openbikesensor/OpenBikeSensor3dPrintableCase/render/thumbnails/LiteCase/LiteSensorSpacer.png

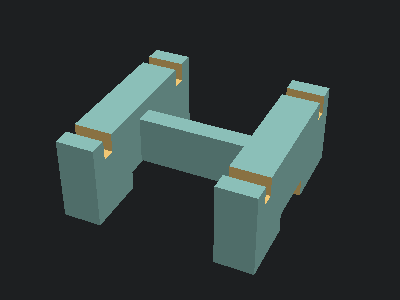
render/thumbnails/LiteCase/LiteSensorSpacer.png
