openbikesensor/OpenBikeSensor3dPrintableCase/MainCase/VerticalCase_JSN-AJ/OBS-MainCase-B-001b_inner_logo_part.stl

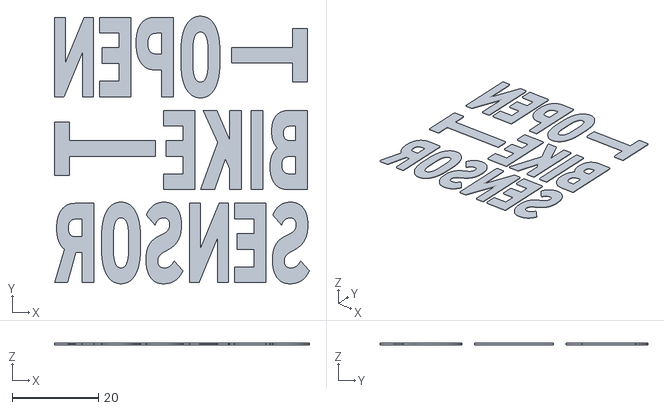
[picture p32: CAD file, 2021-05-19]
MainCase/VerticalCase_JSN-AJ/OBS-MainCase-B-001b_inner_logo_part.stl
59.2 x 62.2 x 0.4
