openbikesensor/OpenBikeSensor3dPrintableCase/MainCase/VerticalCase_JSN-AJ/OBS-MainCase-A-004_GPS-Cover_v0.1.2.stl

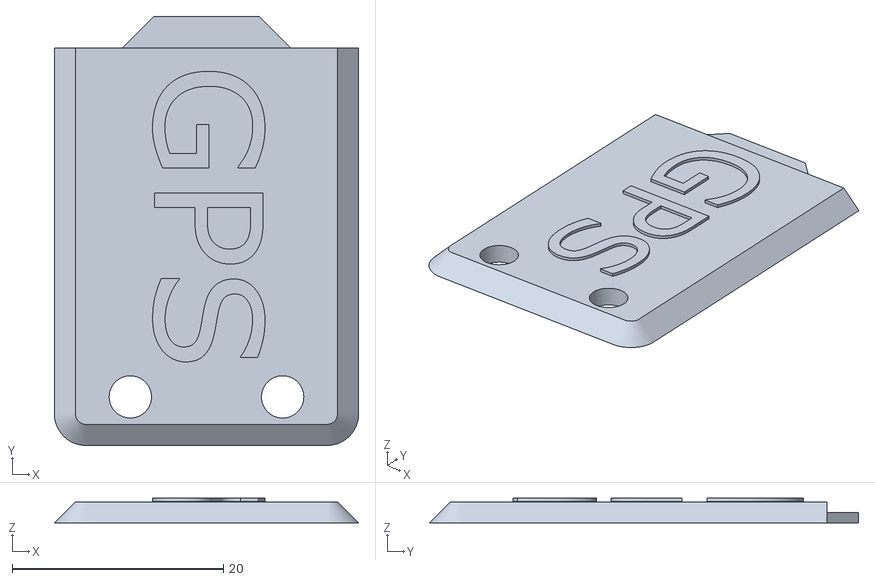
[picture p33: CAD file, 2021-04-24]
MainCase/VerticalCase_JSN-AJ/OBS-MainCase-A-004_GPS-Cover_v0.1.2.stl
28.8 x 40.6 x 2.36
