openbikesensor/OpenBikeSensor3dPrintableCase/MainCase/VerticalCase_JSN-AJ/OBS-MainCase-A-003_USB-Cover_v0.1.1.stl

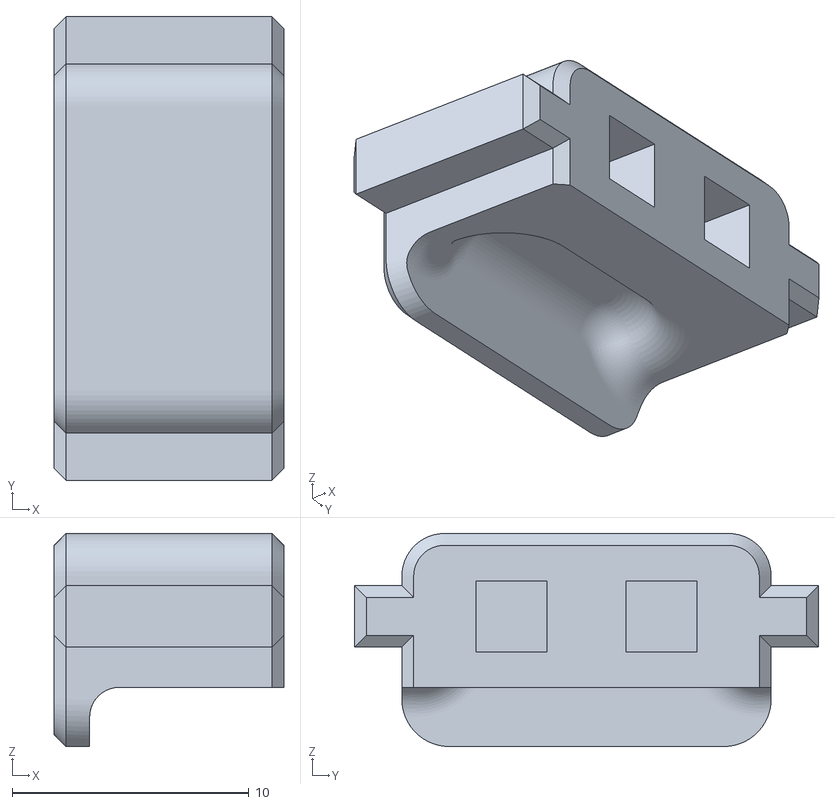
[picture p35: CAD file, 2021-03-09]
MainCase/VerticalCase_JSN-AJ/OBS-MainCase-A-003_USB-Cover_v0.1.1.stl
9.70 x 19.6 x 9.00
