openbikesensor/OpenBikeSensor3dPrintableCase/DisplayCase/DisplayCase32mm/Zwischenstueck.stl

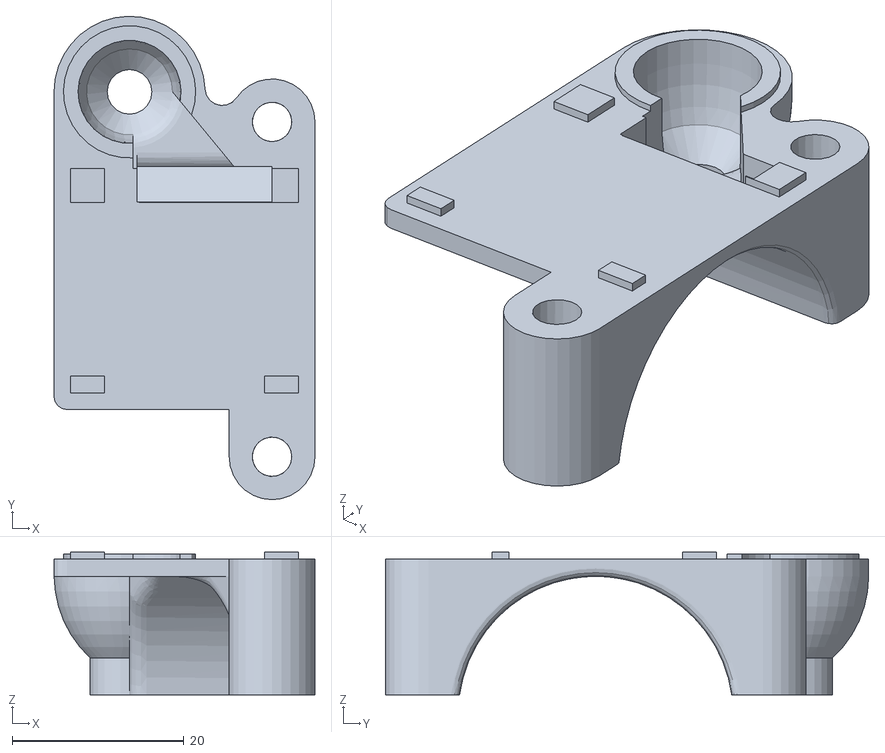
[picture p36: CAD file, 2020-05-23]
DisplayCase/DisplayCase32mm/Zwischenstueck.stl
30.4 x 56.3 x 16.6
