openbikesensor/OpenBikeSensor3dPrintableCase/DisplayCase/experimental/OBS-Kabelbinder-Adapter_kompatibel_zu_OBS-D-003v10.stp

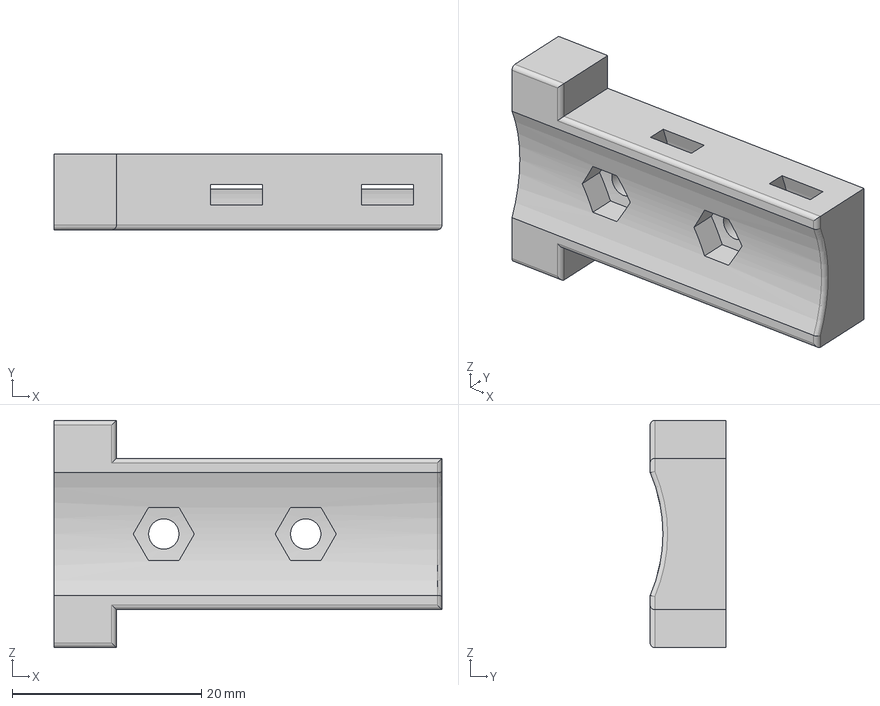
[picture p37: CAD file, 2021-03-13]
DisplayCase/experimental/OBS-Kabelbinder-Adapter_kompatibel_zu_OBS-D-003v10.stp
41.0 x 8.00 x 24.0 mm
