openbikesensor/OpenBikeSensor3dPrintableCase/DisplayCase/PermanentlyMounted/OBS-D-002-V1.step

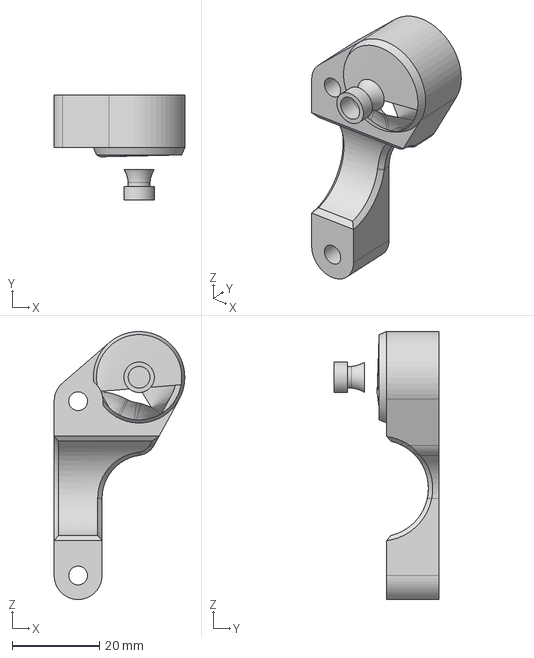
[picture p38: CAD file, 2020-04-30]
DisplayCase/PermanentlyMounted/OBS-D-002-V1.step
30.0 x 24.0 x 61.5 mm
