openbikesensor/OpenBikeSensor3dPrintableCase/DisplayCase/SlideOnDisplay/OBS-Display-A-005_Kabelbinder_Schiene_v0.1.1.stp

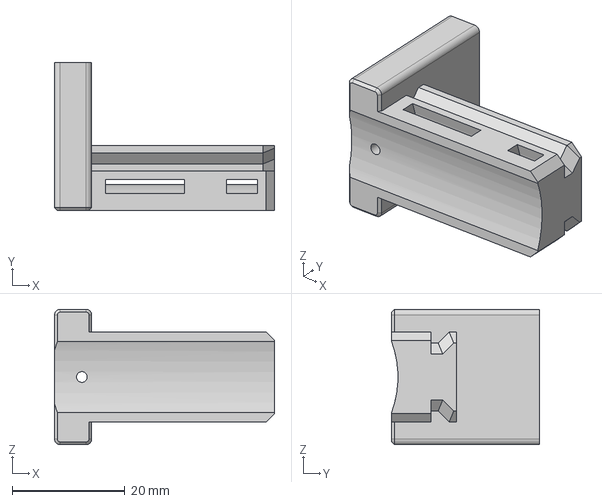
[picture p39: CAD file, 2021-06-07]
DisplayCase/SlideOnDisplay/OBS-Display-A-005_Kabelbinder_Schiene_v0.1.1.stp
39.0 x 26.2 x 24.0 mm
