openbikesensor/OpenBikeSensor3dPrintableCase/DisplayCase/SnapInDisplay/DisplayClip22_2_4mmbrake.stl

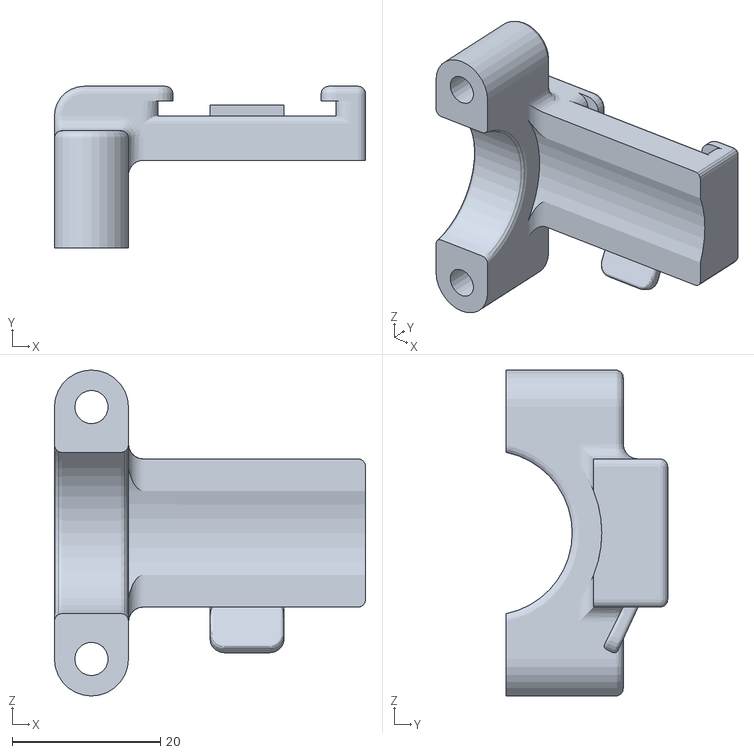
[picture p40: CAD file, 2020-10-29]
DisplayCase/SnapInDisplay/DisplayClip22_2_4mmbrake.stl
42.0 x 21.8 x 44.0
