openbikesensor/OpenBikeSensor3dPrintableCase/export/Calibration/HexNuts.stl

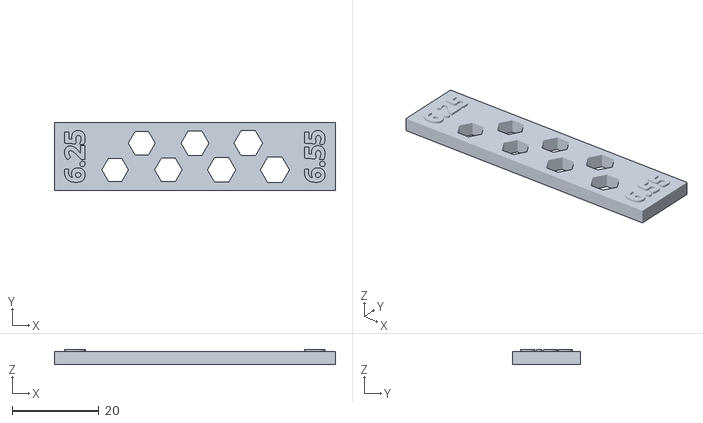
[picture p41: CAD file, 2022-03-04]
export/Calibration/HexNuts.stl
64.9 x 15.7 x 3.50
