openbikesensor/OpenBikeSensor3dPrintableCase/export/DisplayCase/DisplayCaseBottom.stl

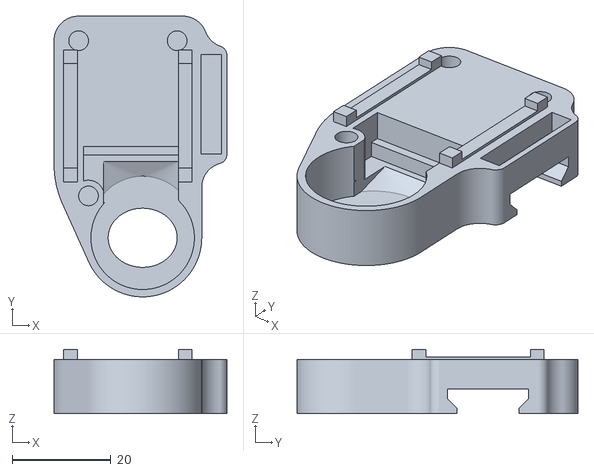
[picture p42: CAD file, 2023-01-06]
export/DisplayCase/DisplayCaseBottom.stl
35.1 x 57.0 x 13.0
