openbikesensor/OpenBikeSensor3dPrintableCase/export/Mounting/BikeRackMountSide.stl

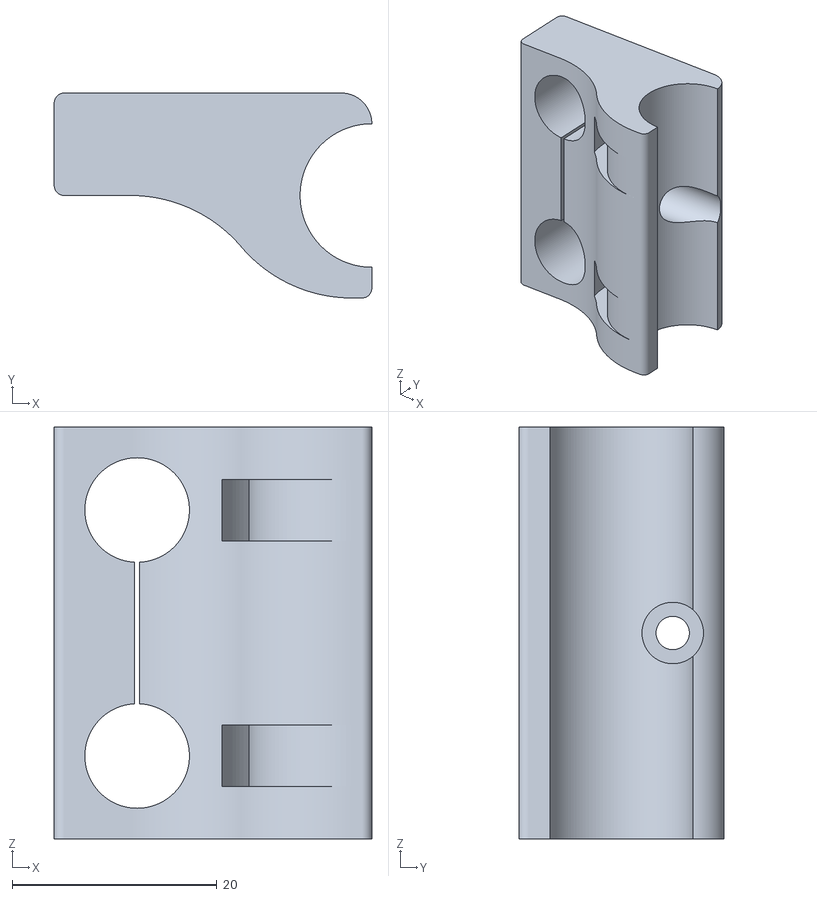
[picture p43: CAD file, 2023-01-06]
export/Mounting/BikeRackMountSide.stl
31.0 x 20.0 x 40.2
