openbikesensor/OpenBikeSensor3dPrintableCase/MainCase/HorizontalCase_JSN-AJ/USB-Deckel.stl

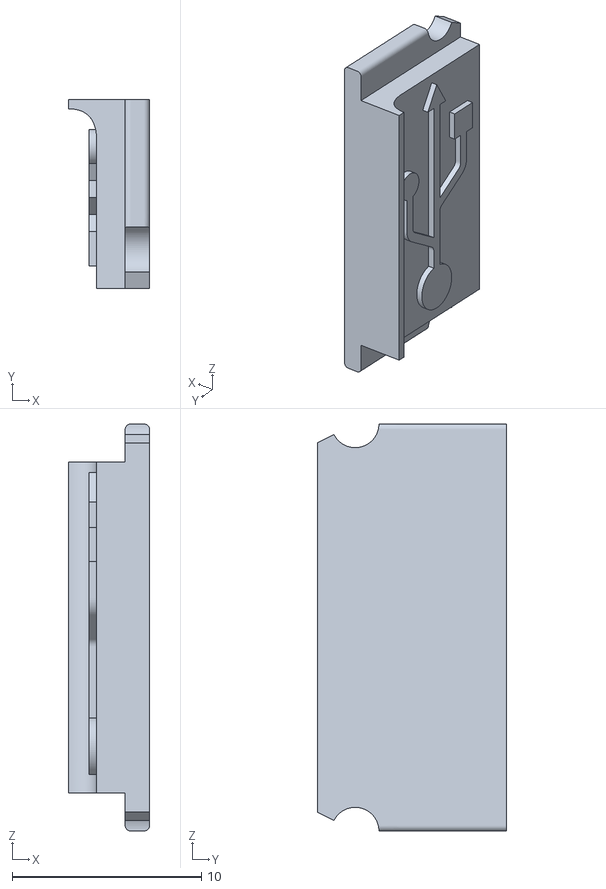
[picture p44: CAD file, 2021-02-20]
MainCase/HorizontalCase_JSN-AJ/USB-Deckel.stl
4.30 x 10.0 x 21.5
