openbikesensor/OpenBikeSensor3dPrintableCase/MainCase/SnapInCase/SaddleClipPart2_wide.stl

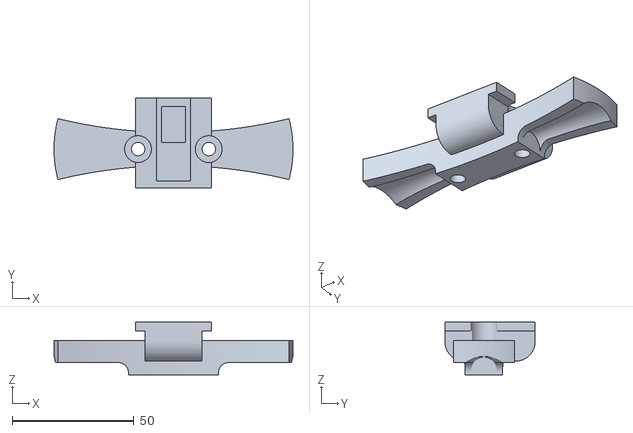
[picture p45: CAD file, 2020-10-19]
MainCase/SnapInCase/SaddleClipPart2_wide.stl
98.0 x 37.0 x 21.6
