openbikesensor/OpenBikeSensor3dPrintableCase/MainCase/TopTubeCase/OBS-C-005-V1.step

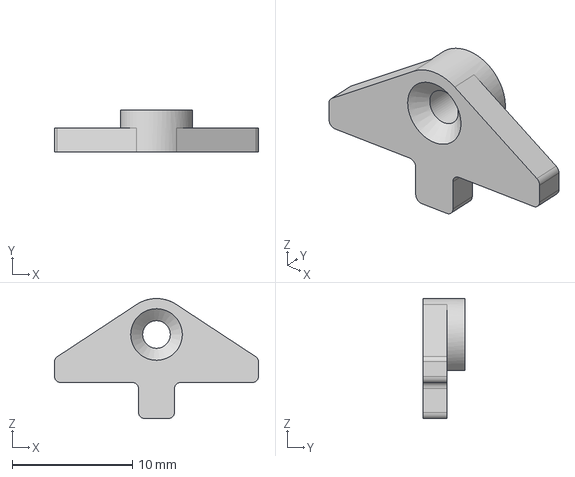
[picture p46: CAD file, 2020-04-30]
MainCase/TopTubeCase/OBS-C-005-V1.step
17.0 x 3.50 x 10.0 mm
