openbikesensor/OpenBikeSensor3dPrintableCase/Various/PCB00.03-SensorDistanceClip.stl

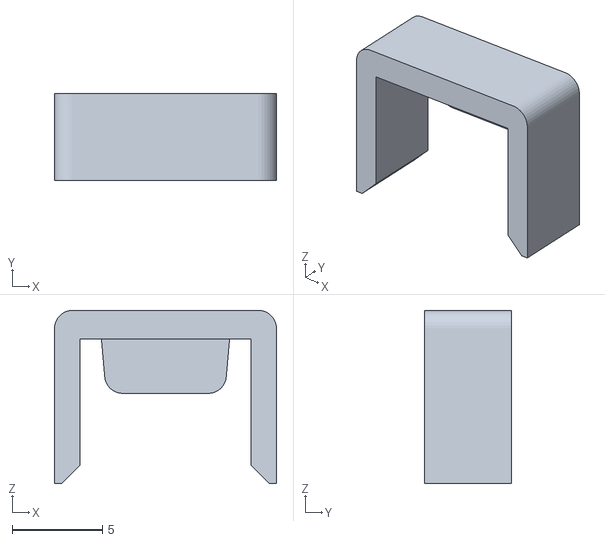
[picture p47: CAD file, 2021-03-15]
Various/PCB00.03-SensorDistanceClip.stl
12.3 x 4.80 x 9.60
