openbikesensor/OpenBikeSensor3dPrintableCase/DisplayCase/DisplayCase32mm/Oberschale.stl

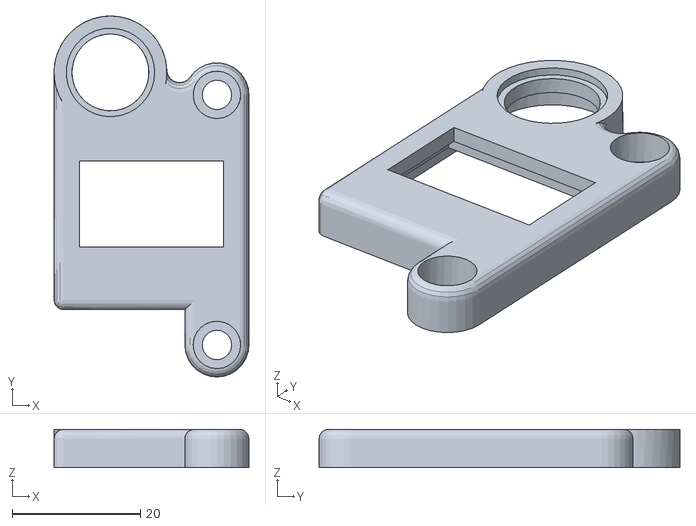
[picture p48: CAD file, 2020-05-23]
DisplayCase/DisplayCase32mm/Oberschale.stl
30.4 x 56.3 x 6.00
