openbikesensor/OpenBikeSensor3dPrintableCase/DisplayCase/experimental/OBS-Kabelbinder-Adapter_kompatibel_zu_OBS-D-003v10_schmal.stp

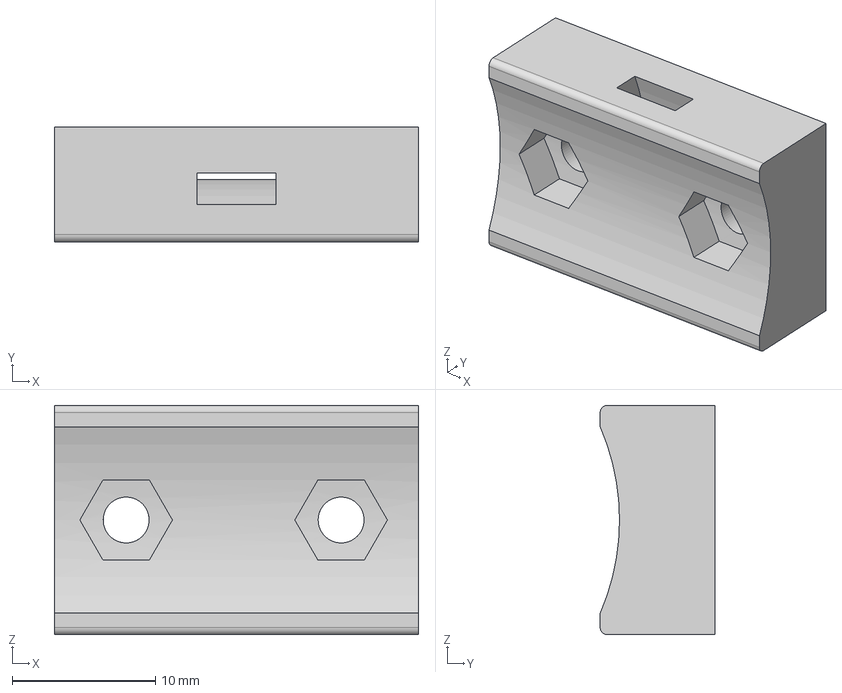
[picture p49: CAD file, 2021-03-13]
DisplayCase/experimental/OBS-Kabelbinder-Adapter_kompatibel_zu_OBS-D-003v10_schmal.stp
25.4 x 8.00 x 16.0 mm
