openbikesensor/OpenBikeSensor3dPrintableCase/DisplayCase/PermanentlyMounted/OBS-D-004-V1.step

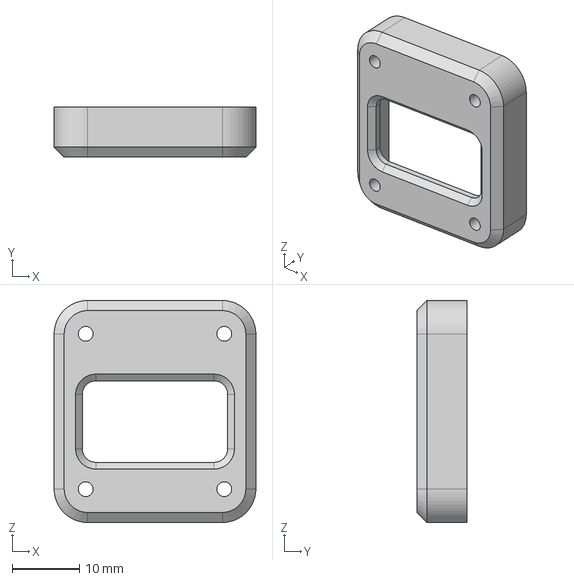
[picture p50: CAD file, 2020-04-30]
DisplayCase/PermanentlyMounted/OBS-D-004-V1.step
30.0 x 7.50 x 33.0 mm
