openbikesensor/OpenBikeSensor3dPrintableCase/DisplayCase/SlideOnDisplay/OBS-Display-A-002_HeatSetInsert_Display_Bottom_v0.1.0.stp

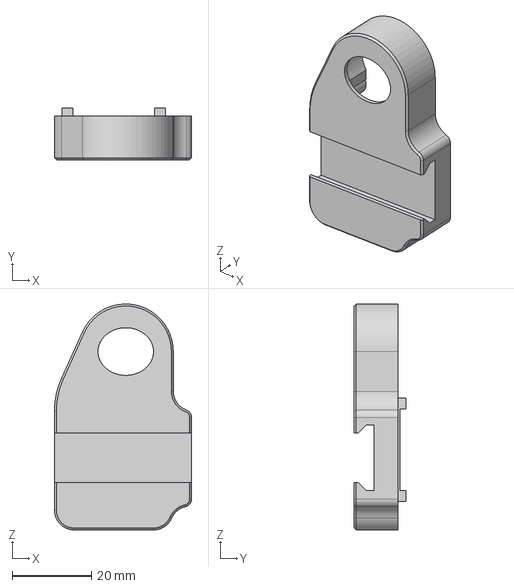
[picture p51: CAD file, 2021-04-29]
DisplayCase/SlideOnDisplay/OBS-Display-A-002_HeatSetInsert_Display_Bottom_v0.1.0.stp
34.6 x 13.0 x 57.0 mm
