openbikesensor/OpenBikeSensor3dPrintableCase/DisplayCase/SnapInDisplay/Bracket22_2.stl

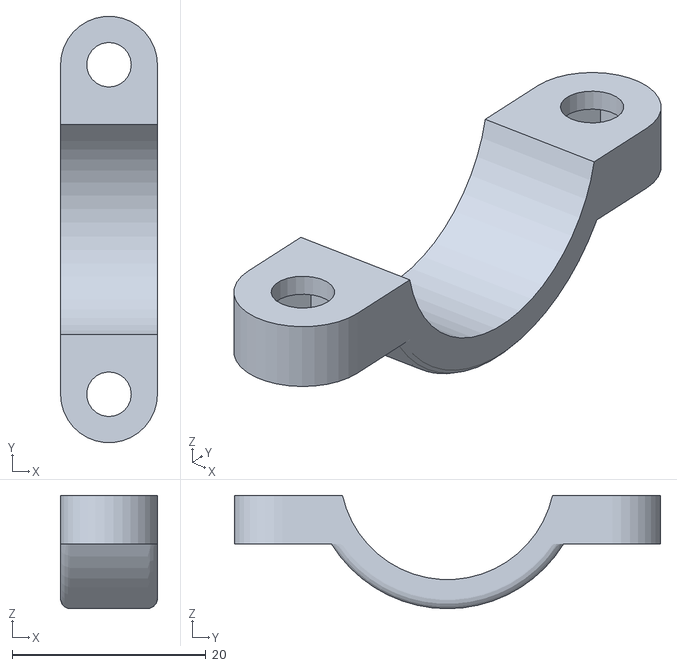
[picture p52: CAD file, 2020-10-29]
DisplayCase/SnapInDisplay/Bracket22_2.stl
10.0 x 44.0 x 11.7
