openbikesensor/OpenBikeSensor3dPrintableCase/export/Calibration/SteppingXY.stl

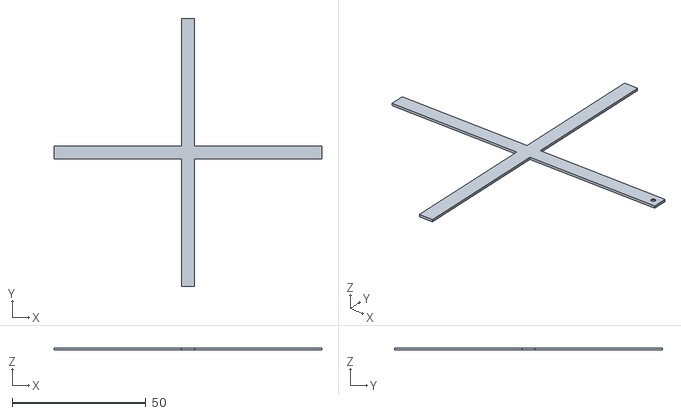
[picture p53: CAD file, 2022-03-04]
export/Calibration/SteppingXY.stl
100.0 x 100.0 x 0.8
