openbikesensor/OpenBikeSensor3dPrintableCase/export/DisplayCase/DisplayCaseTop.stl

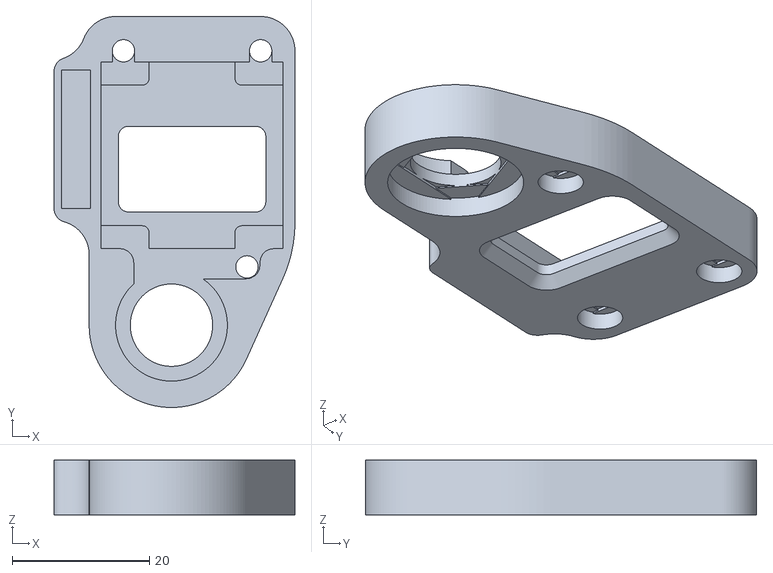
[picture p54: CAD file, 2023-01-06]
export/DisplayCase/DisplayCaseTop.stl
35.1 x 57.0 x 8.00
