openbikesensor/OpenBikeSensor3dPrintableCase/export/MainCase/GpsAntennaLid.stl

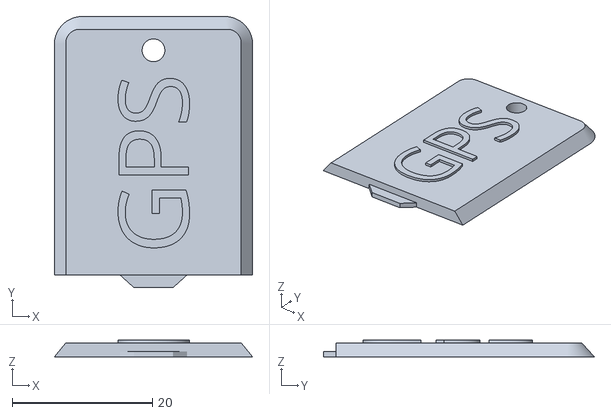
[picture p55: CAD file, 2023-01-06]
export/MainCase/GpsAntennaLid.stl
28.3 x 38.6 x 2.40
