openbikesensor/OpenBikeSensor3dPrintableCase/export/Mounting/HandlebarRail.stl

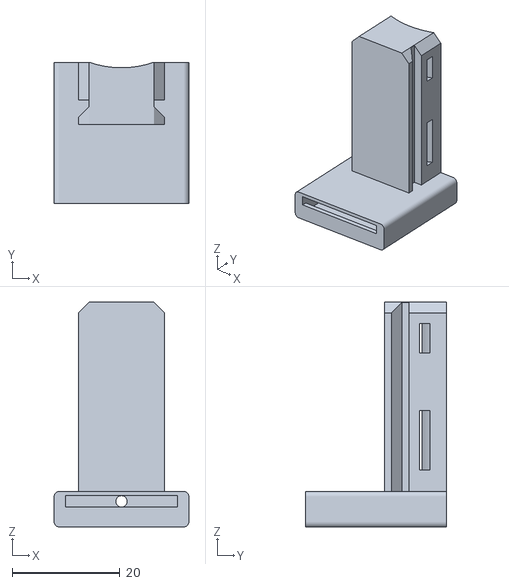
[picture p56: CAD file, 2023-01-06]
export/Mounting/HandlebarRail.stl
25.0 x 26.2 x 41.7
