openbikesensor/OpenBikeSensor3dPrintableCase/MainCase/HorizontalCase_JSN-AJ/SaddleClipPart1.stp

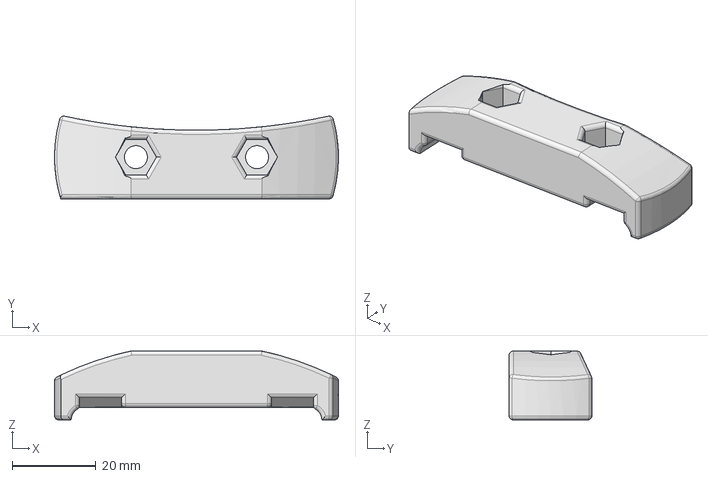
[picture p57: CAD file, 2020-10-19]
MainCase/HorizontalCase_JSN-AJ/SaddleClipPart1.stp
68.0 x 19.8 x 16.5 mm
