openbikesensor/OpenBikeSensor3dPrintableCase/MainCase/SnapInCase/SaddleClipPart2.stp

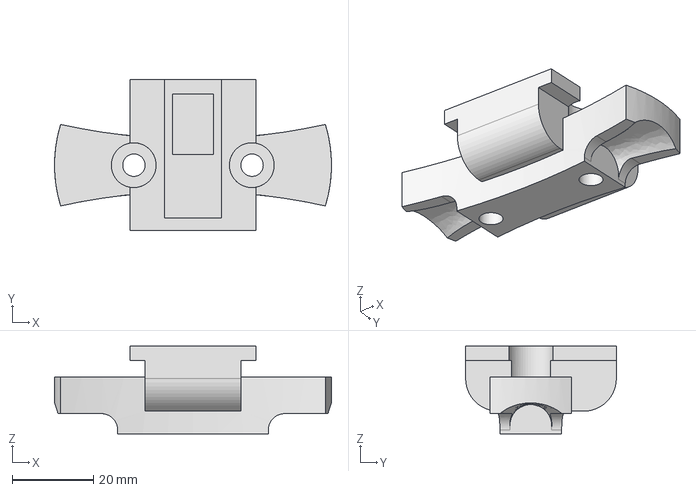
[picture p58: CAD file, 2020-06-22]
MainCase/SnapInCase/SaddleClipPart2.stp
68.0 x 37.0 x 21.6 mm
