openbikesensor/OpenBikeSensor3dPrintableCase/MainCase/TopTubeCase/OBS-C-007-V1.step

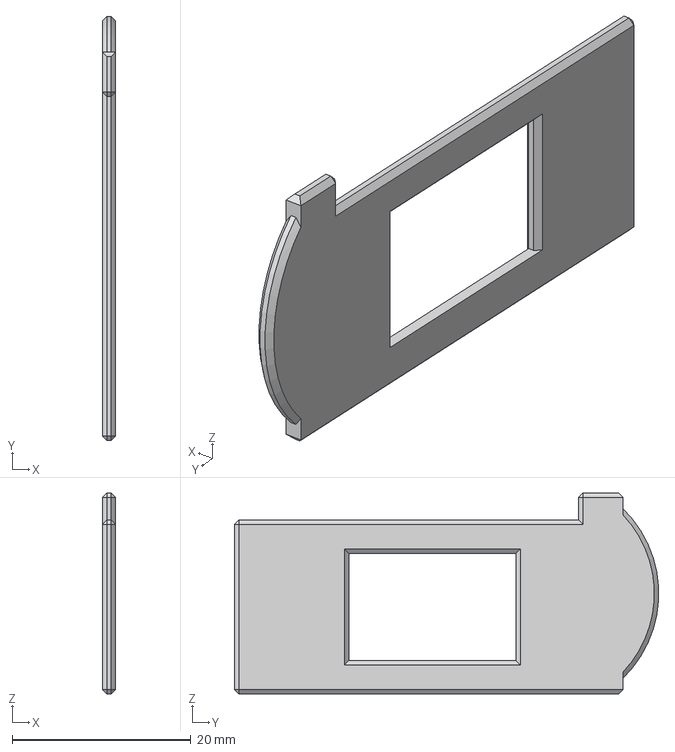
[picture p59: CAD file, 2020-04-30]
MainCase/TopTubeCase/OBS-C-007-V1.step
1.50 x 47.5 x 22.5 mm
