openbikesensor/OpenBikeSensor3dPrintableCase/DisplayCase/DisplayCase32mm/Schelle32.stl

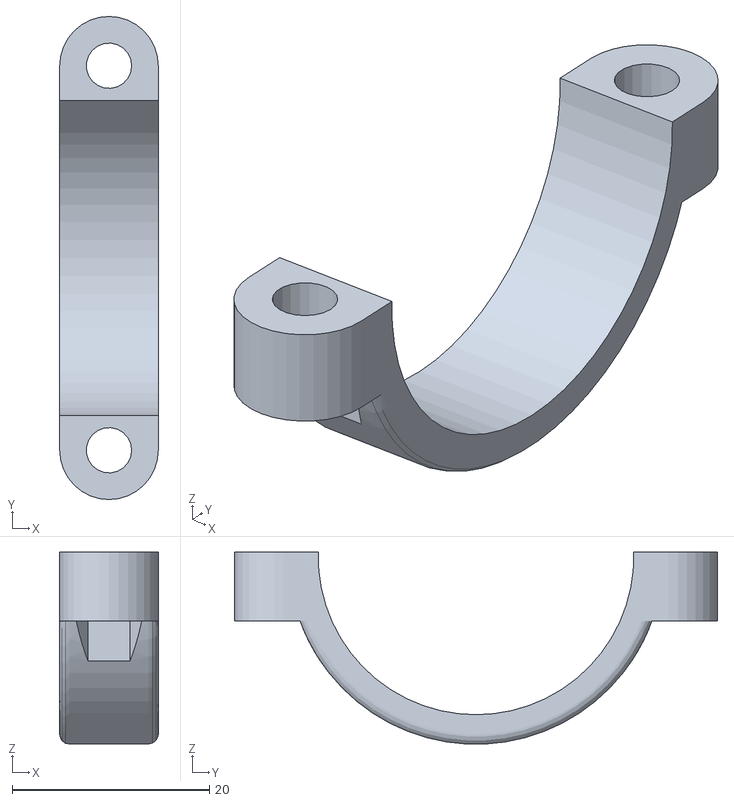
[picture p60: CAD file, 2020-05-23]
DisplayCase/DisplayCase32mm/Schelle32.stl
10.0 x 49.0 x 19.5
