openbikesensor/OpenBikeSensor3dPrintableCase/DisplayCase/experimental/90deg_top_v2.stl

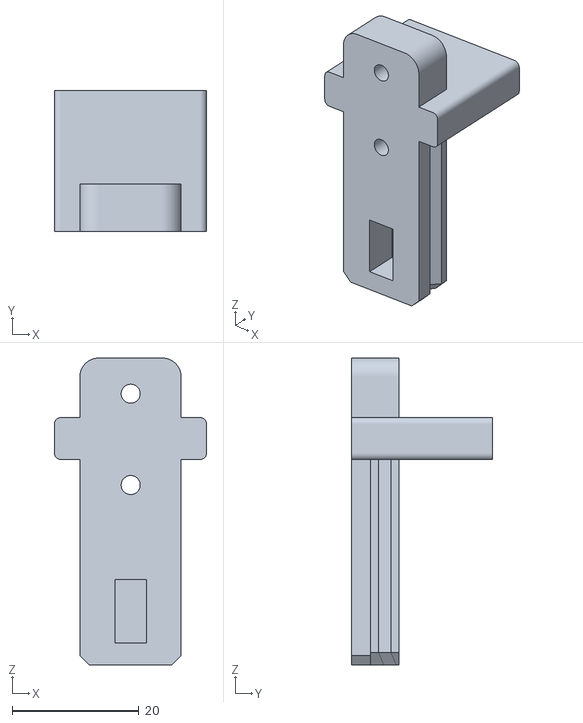
[picture p61: CAD file, 2021-03-11]
DisplayCase/experimental/90deg_top_v2.stl
24.0 x 22.2 x 48.4
