openbikesensor/OpenBikeSensor3dPrintableCase/DisplayCase/PermanentlyMounted/OBS-D-005-V1.step

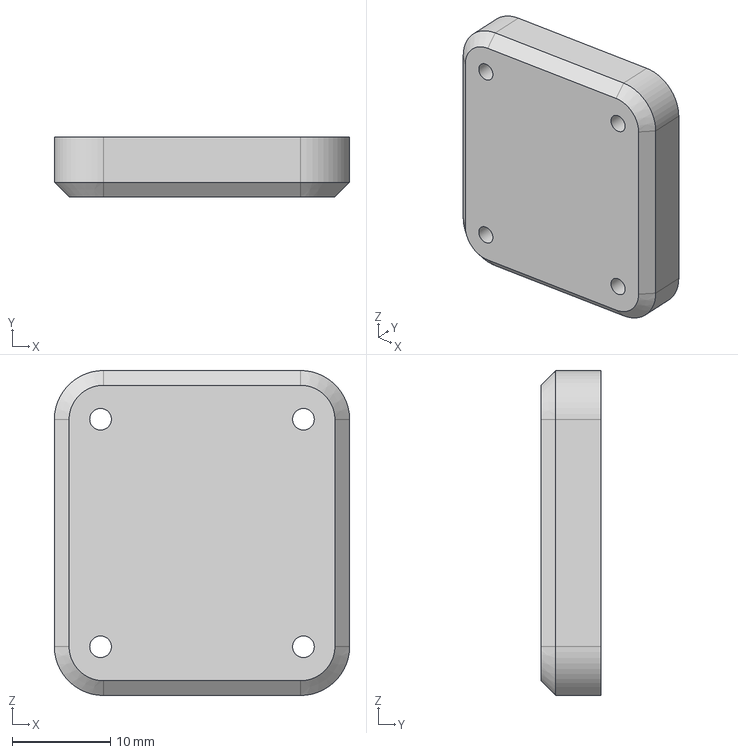
[picture p62: CAD file, 2020-04-30]
DisplayCase/PermanentlyMounted/OBS-D-005-V1.step
30.0 x 6.10 x 33.0 mm
