openbikesensor/OpenBikeSensor3dPrintableCase/DisplayCase/SlideOnDisplay/OBS-Display-B-005_Schiene_v0.1.0.stp

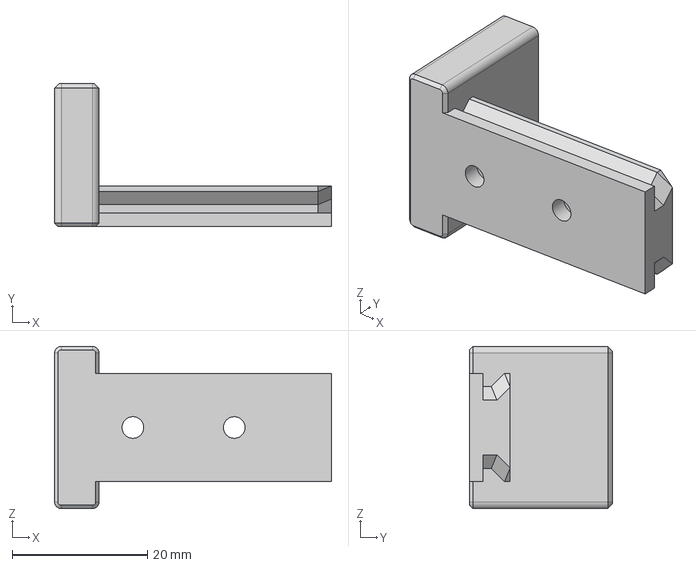
[picture p63: CAD file, 2021-04-29]
DisplayCase/SlideOnDisplay/OBS-Display-B-005_Schiene_v0.1.0.stp
41.0 x 21.2 x 24.0 mm
