openbikesensor/OpenBikeSensor3dPrintableCase/DisplayCase/SnapInDisplay/DisplayClip32.stp

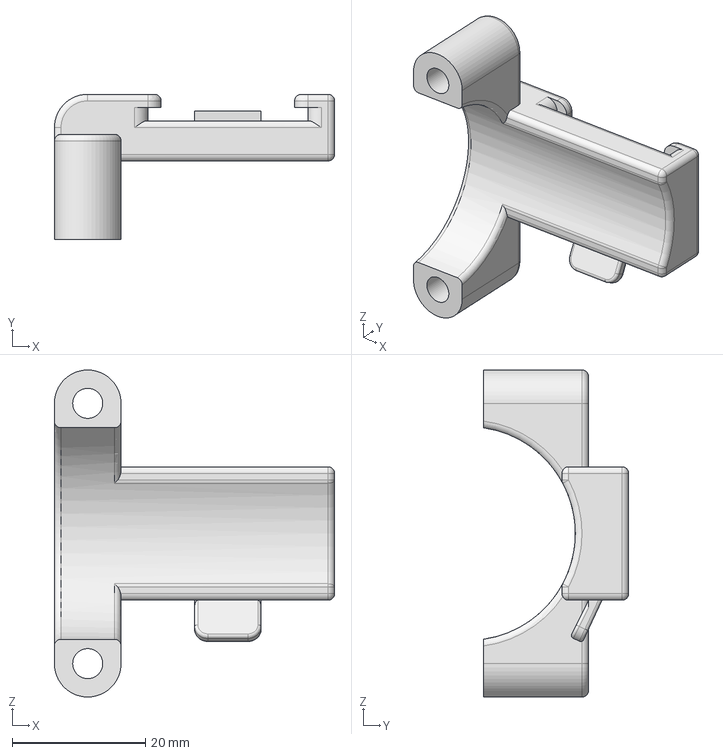
[picture p64: CAD file, 2020-10-02]
DisplayCase/SnapInDisplay/DisplayClip32.stp
42.0 x 21.8 x 49.0 mm
