openbikesensor/OpenBikeSensor3dPrintableCase/export/DisplayCase/DisplayCableStrainRelief.stl

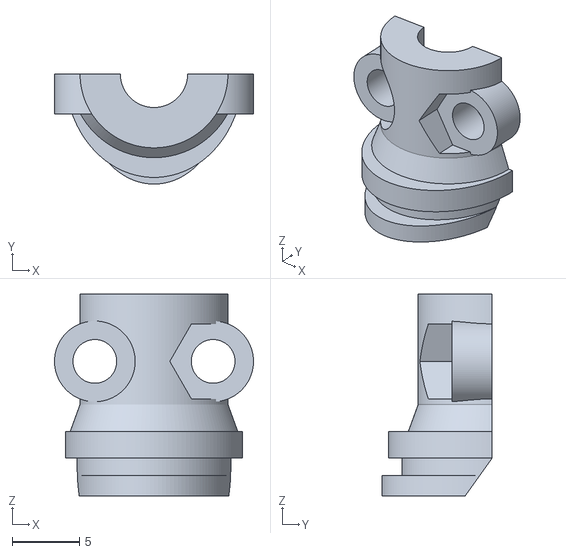
[picture p65: CAD file, 2022-03-15]
export/DisplayCase/DisplayCableStrainRelief.stl
14.8 x 8.20 x 15.0
