openbikesensor/OpenBikeSensor3dPrintableCase/export/MainCase/UsbCover.stl

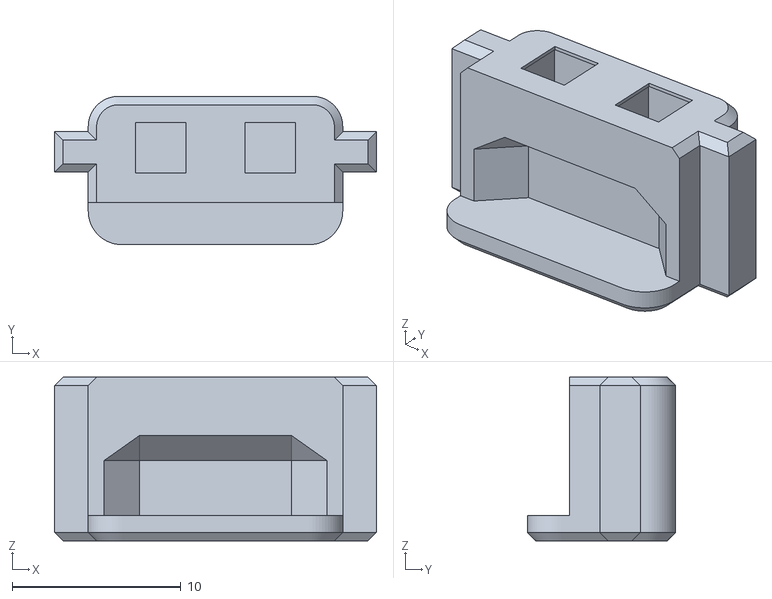
[picture p66: CAD file, 2022-07-26]
export/MainCase/UsbCover.stl
19.1 x 8.80 x 9.70
