openbikesensor/OpenBikeSensor3dPrintableCase/export/Mounting/BikeRackMountCenterLongitudinal.stl

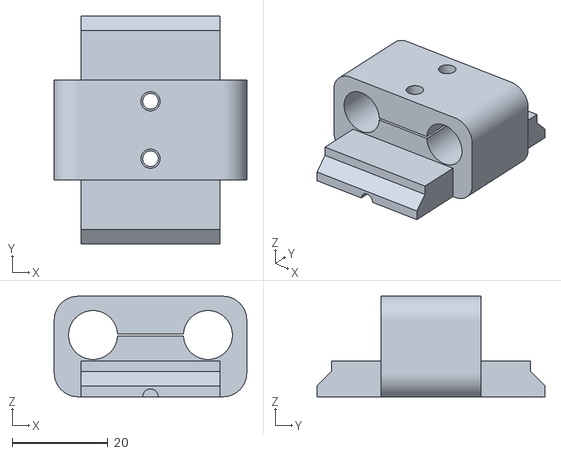
[picture p67: CAD file, 2023-01-06]
export/Mounting/BikeRackMountCenterLongitudinal.stl
40.2 x 47.6 x 21.0
