openbikesensor/OpenBikeSensor3dPrintableCase/MainCase/HorizontalCase_JSN-AJ/SaddleClipPart1_wide.stl

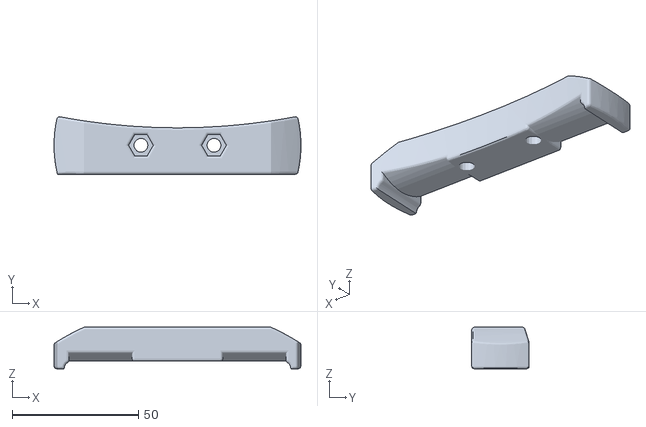
[picture p68: CAD file, 2020-10-19]
MainCase/HorizontalCase_JSN-AJ/SaddleClipPart1_wide.stl
98.0 x 22.8 x 16.5
