openbikesensor/OpenBikeSensor3dPrintableCase/MainCase/SnapInCase/OBS-SnapInCase_light.stp

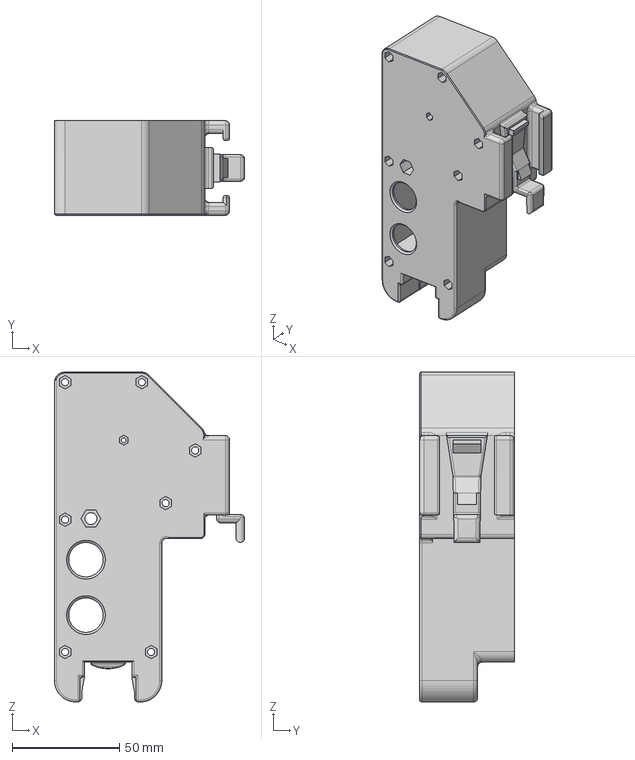
[picture p69: CAD file, 2020-06-22]
MainCase/SnapInCase/OBS-SnapInCase_light.stp
88.5 x 44.0 x 153.5 mm
