openbikesensor/OpenBikeSensor3dPrintableCase/MainCase/TopTubeCase/OBS-C-004-V1.step

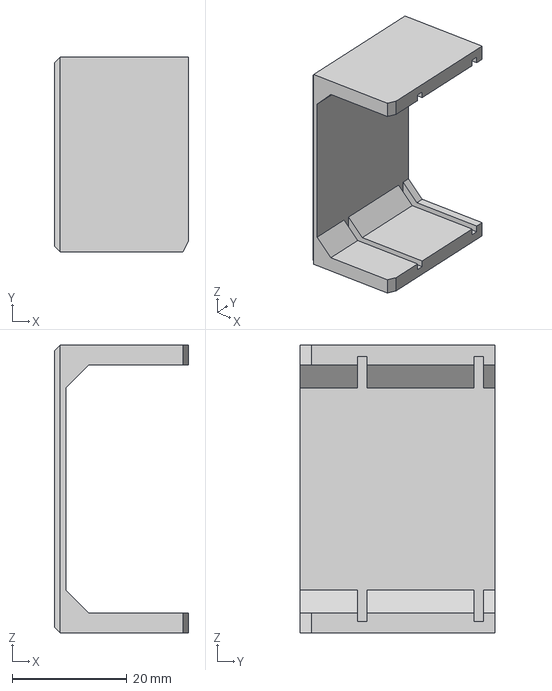
[picture p70: CAD file, 2020-04-30]
MainCase/TopTubeCase/OBS-C-004-V1.step
23.4 x 34.0 x 50.2 mm
