openbikesensor/OpenBikeSensor3dPrintableCase/DisplayCase/experimental/90deg_bottom_v2.stl

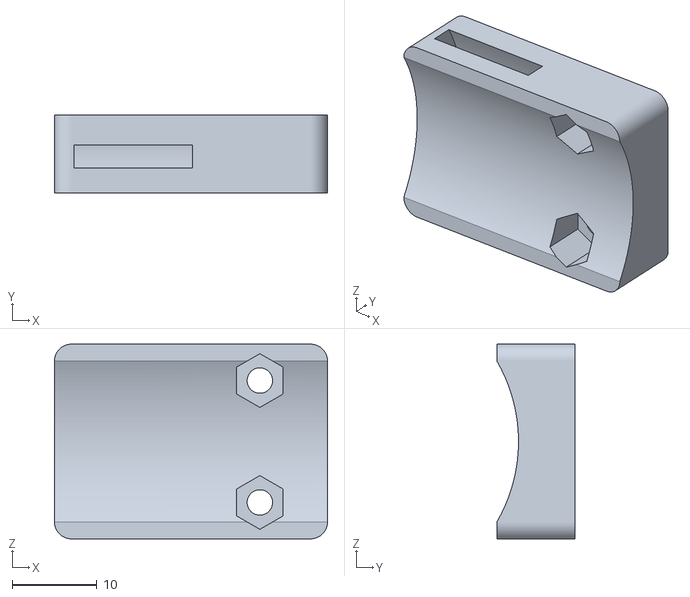
[picture p71: CAD file, 2021-03-11]
DisplayCase/experimental/90deg_bottom_v2.stl
32.3 x 9.25 x 23.0
