openbikesensor/OpenBikeSensor3dPrintableCase/DisplayCase/PermanentlyMounted/OBS-D-001-V1.step

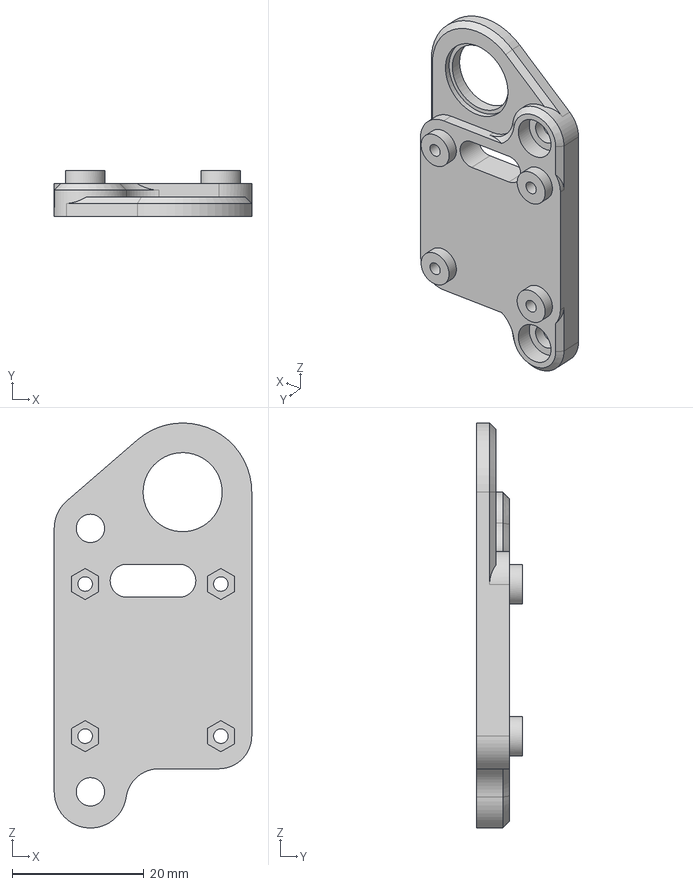
[picture p72: CAD file, 2020-04-30]
DisplayCase/PermanentlyMounted/OBS-D-001-V1.step
30.0 x 7.00 x 61.5 mm
