openbikesensor/OpenBikeSensor3dPrintableCase/DisplayCase/SlideOnDisplay/OBS-Display-A-003_Zugentlastung_v0.1.1.stl

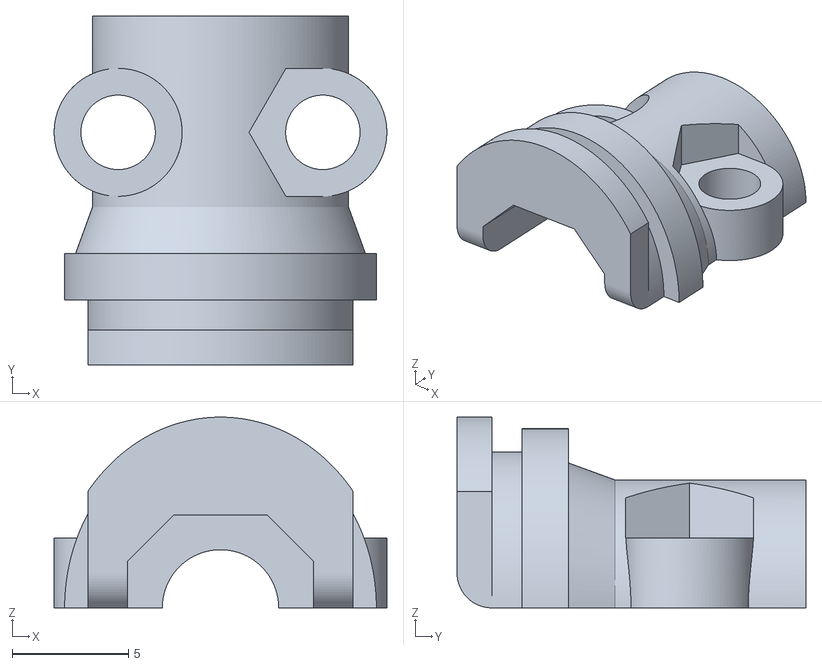
[picture p73: CAD file, 2021-04-29]
DisplayCase/SlideOnDisplay/OBS-Display-A-003_Zugentlastung_v0.1.1.stl
14.3 x 15.0 x 8.20
