openbikesensor/OpenBikeSensor3dPrintableCase/DisplayCase/SnapInDisplay/DisplayClipLid.stp

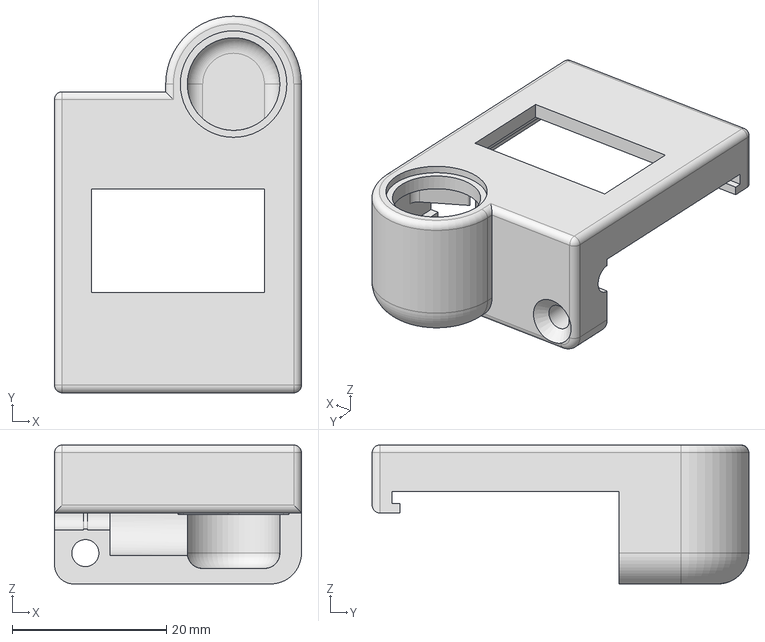
[picture p74: CAD file, 2020-07-24]
DisplayCase/SnapInDisplay/DisplayClipLid.stp
32.0 x 48.8 x 18.0 mm
