openbikesensor/OpenBikeSensor3dPrintableCase/export/Mounting/DisplayMagnetDummy.stl

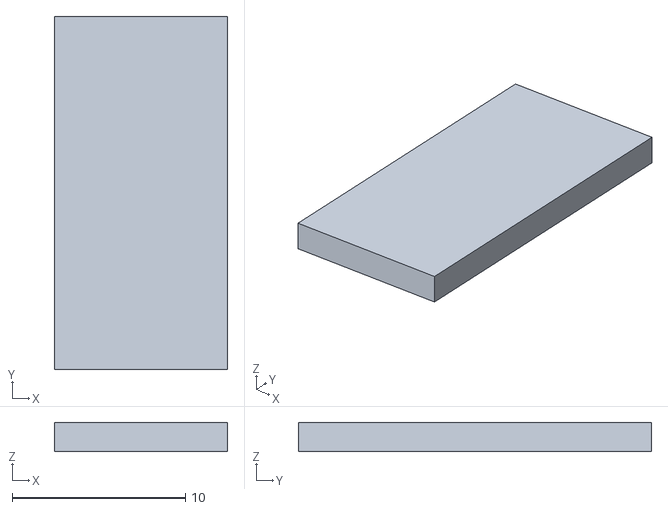
[picture p75: CAD file, 2023-01-06]
export/Mounting/DisplayMagnetDummy.stl
10.0 x 20.4 x 1.70
