openbikesensor/OpenBikeSensor3dPrintableCase/MainCase/HorizontalCase_JSN-AJ/Deckel_Logo.stl

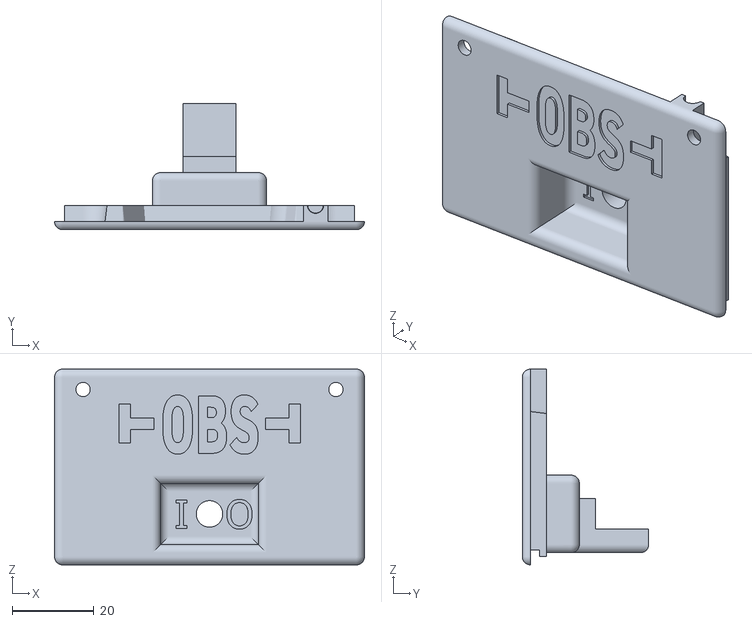
[picture p76: CAD file, 2020-10-19]
MainCase/HorizontalCase_JSN-AJ/Deckel_Logo.stl
76.0 x 31.0 x 48.0
