openbikesensor/OpenBikeSensor3dPrintableCase/MainCase/SnapInCase/OBS-SnapInPCBHolder.stp

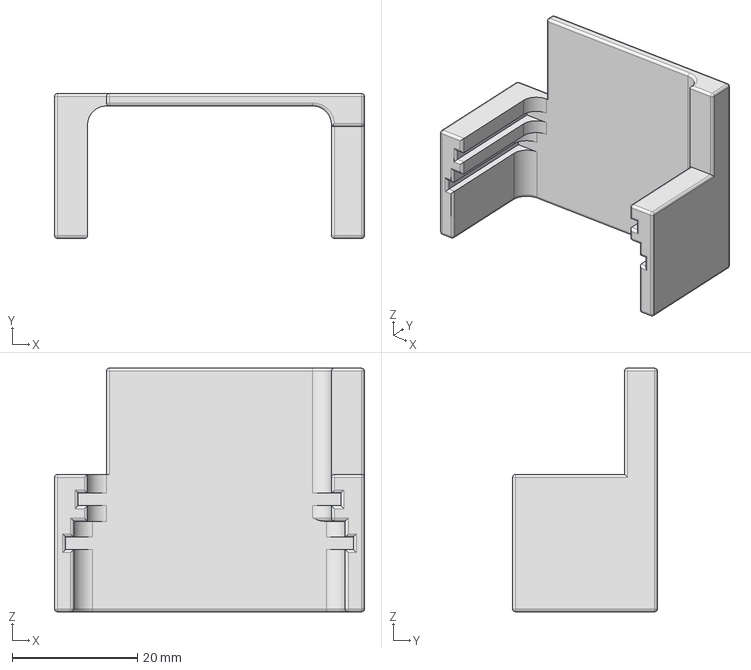
[picture p77: CAD file, 2020-06-22]
MainCase/SnapInCase/OBS-SnapInPCBHolder.stp
49.6 x 23.2 x 39.0 mm
