openbikesensor/OpenBikeSensor3dPrintableCase/MainCase/TopTubeCase/OBS-C-006-V1.step

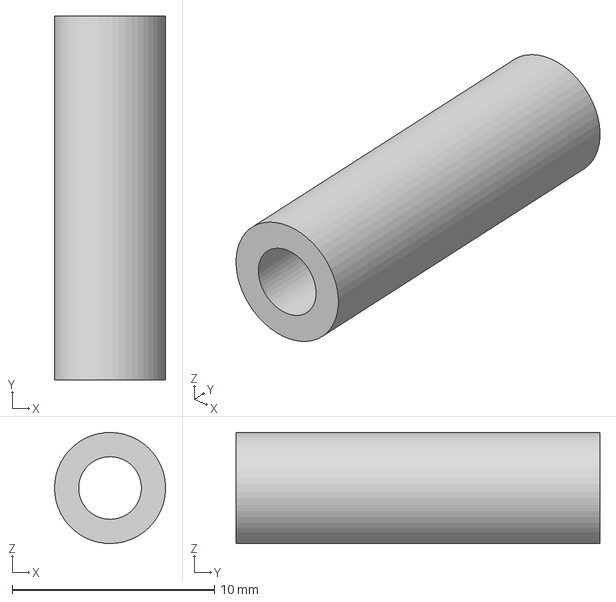
[picture p78: CAD file, 2020-04-30]
MainCase/TopTubeCase/OBS-C-006-V1.step
5.49 x 18.0 x 5.50 mm
