openbikesensor/OpenBikeSensor3dPrintableCase/DisplayCase/experimental/90deg_top.step

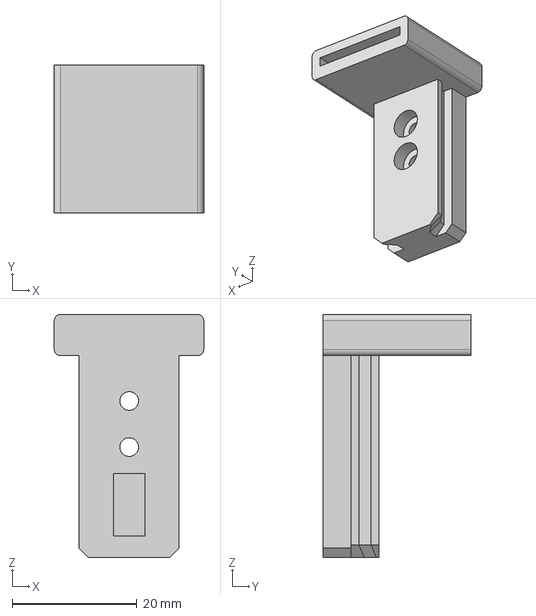
[picture p79: CAD file, 2021-03-01]
DisplayCase/experimental/90deg_top.step
24.0 x 23.7 x 39.0 mm
