openbikesensor/OpenBikeSensor3dPrintableCase/DisplayCase/PermanentlyMounted/OBS-D-003-V1.step

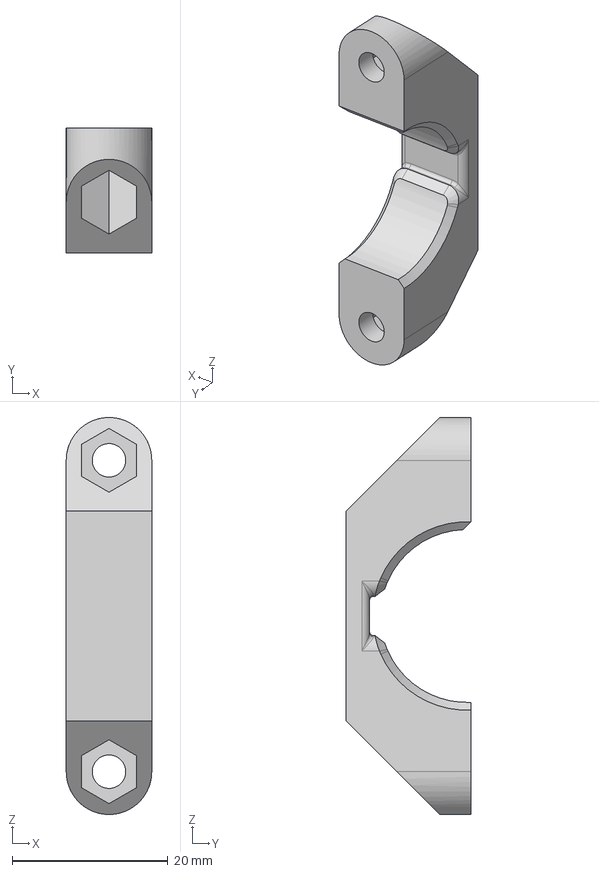
[picture p80: CAD file, 2020-04-30]
DisplayCase/PermanentlyMounted/OBS-D-003-V1.step
11.0 x 16.0 x 51.0 mm
