openbikesensor/OpenBikeSensor3dPrintableCase/DisplayCase/SnapInDisplay/DisplayClip26_8.stp

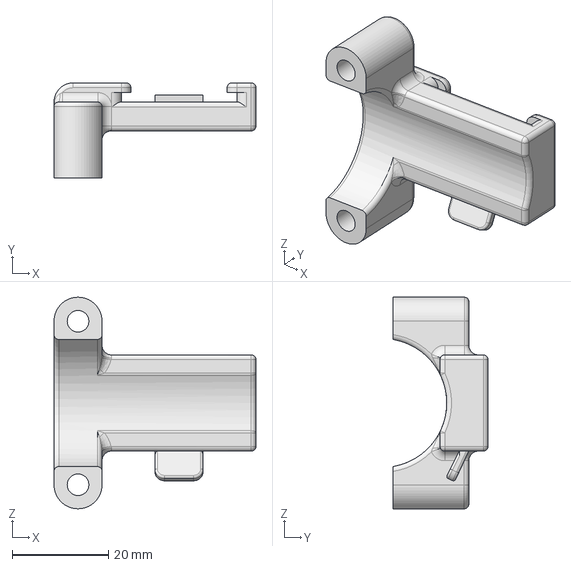
[picture p81: CAD file, 2020-07-15]
DisplayCase/SnapInDisplay/DisplayClip26_8.stp
42.0 x 19.8 x 44.0 mm
