openbikesensor/OpenBikeSensor3dPrintableCase/export/Mounting/BikeRackMountCenter.stl

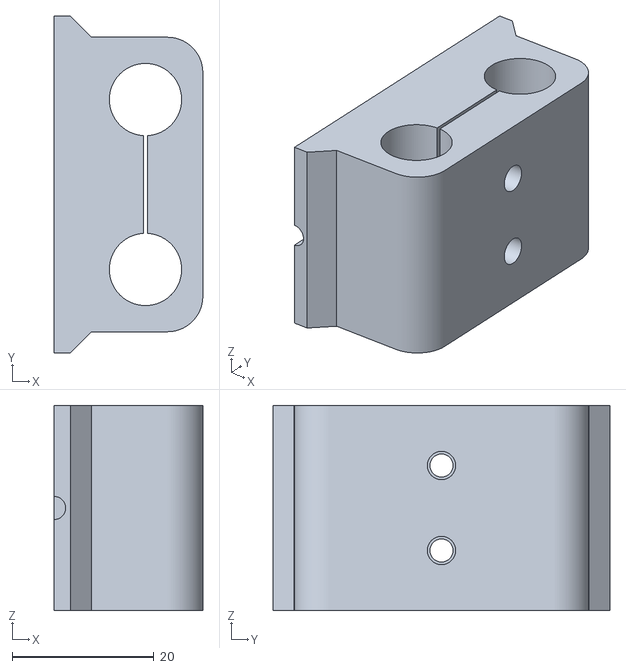
[picture p82: CAD file, 2023-01-06]
export/Mounting/BikeRackMountCenter.stl
21.0 x 47.6 x 29.0
