openbikesensor/OpenBikeSensor3dPrintableCase/MainCase/HorizontalCase_JSN-AJ/GehaeuseFlach_Logo.stl

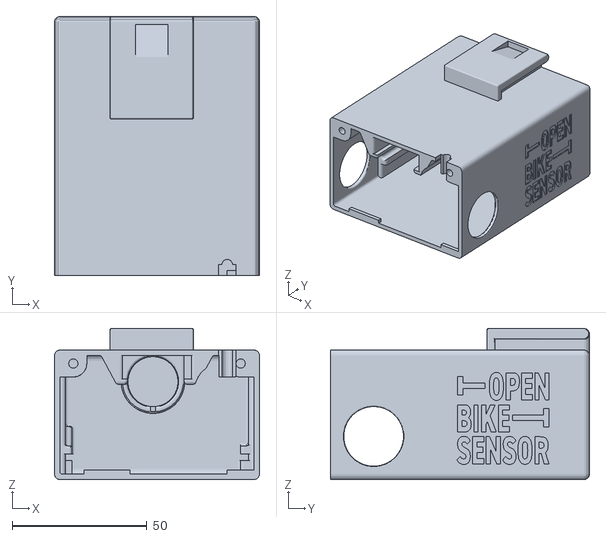
[picture p83: CAD file, 2020-10-19]
MainCase/HorizontalCase_JSN-AJ/GehaeuseFlach_Logo.stl
76.0 x 96.0 x 56.0
