openbikesensor/OpenBikeSensor3dPrintableCase/MainCase/TopTubeCase/OBS-C-001-V1.step

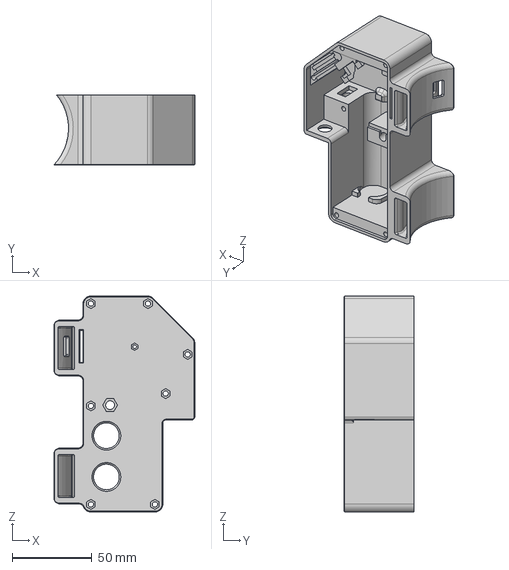
[picture p84: CAD file, 2020-04-30]
MainCase/TopTubeCase/OBS-C-001-V1.step
88.0 x 44.0 x 135.0 mm
