openbikesensor/OpenBikeSensor3dPrintableCase/MainCase/VerticalCase_JSN-AJ/experimental/OBS-C-001-HeatSetInserts.stp

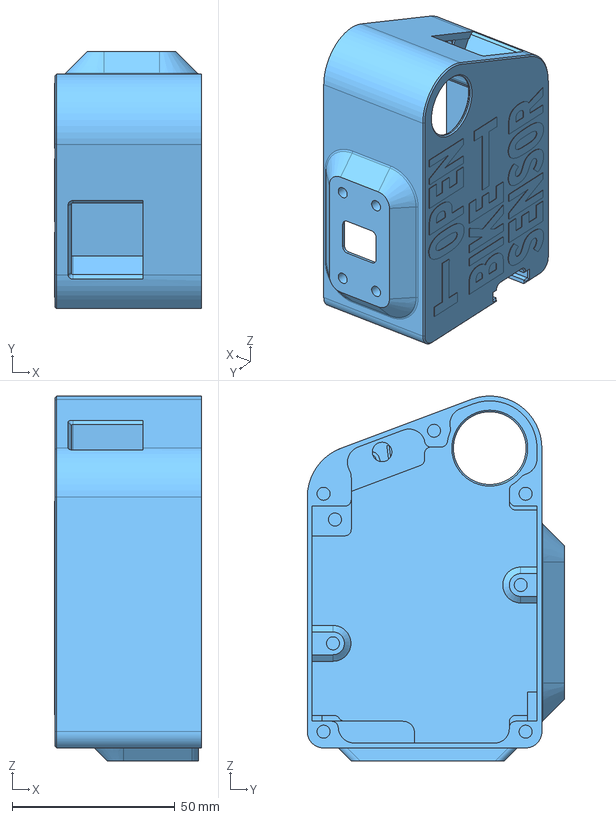
[picture p85: CAD file, 2021-03-18]
MainCase/VerticalCase_JSN-AJ/experimental/OBS-C-001-HeatSetInserts.stp
45.2 x 79.0 x 112.0 mm
