openbikesensor/OpenBikeSensor3dPrintableCase/DisplayCase/experimental/90deg_bottom.step

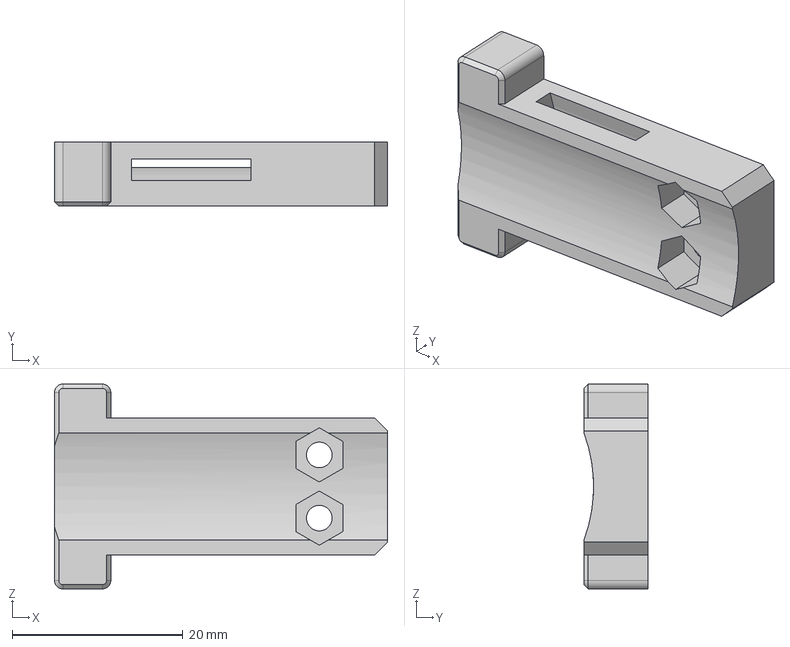
[picture p86: CAD file, 2021-03-01]
DisplayCase/experimental/90deg_bottom.step
39.0 x 7.50 x 24.0 mm
