openbikesensor/OpenBikeSensor3dPrintableCase/DisplayCase/SlideOnDisplay/OBS-Display-C-006_Kabelbinder_Halter_gedreht_v0.1.0.stp

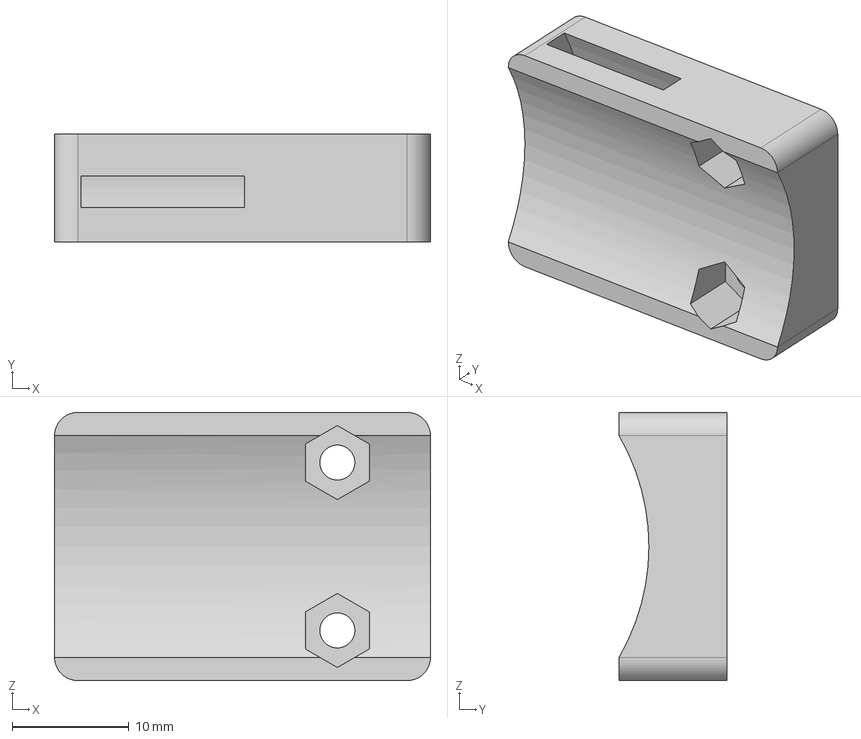
[picture p87: CAD file, 2021-04-29]
DisplayCase/SlideOnDisplay/OBS-Display-C-006_Kabelbinder_Halter_gedreht_v0.1.0.stp
32.2 x 9.25 x 23.0 mm
