openbikesensor/OpenBikeSensor3dPrintableCase/DisplayCase/SnapInDisplay/Bracket26_8.stp

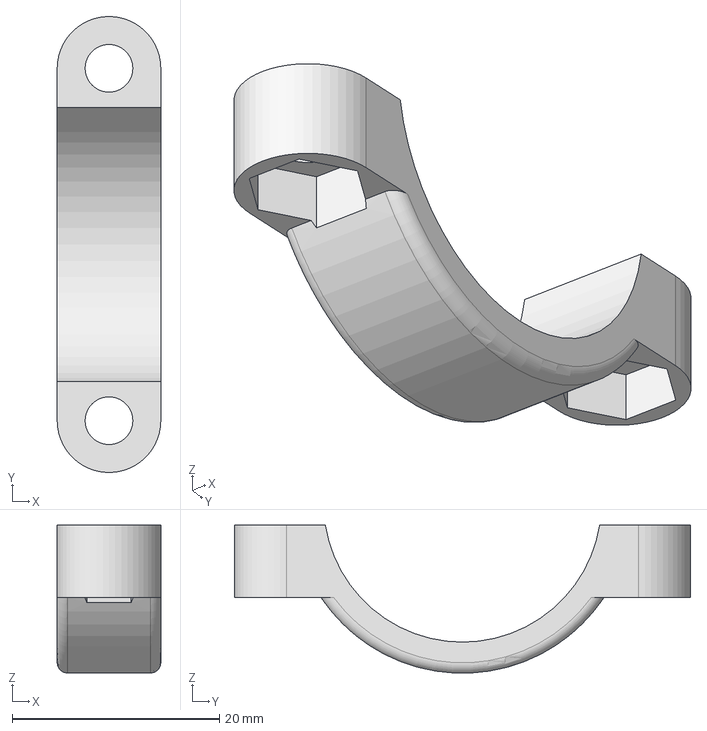
[picture p88: CAD file, 2020-07-15]
DisplayCase/SnapInDisplay/Bracket26_8.stp
10.0 x 44.0 x 14.3 mm
