openbikesensor/OpenBikeSensor3dPrintableCase/export/Mounting/TopTubeMount.stl

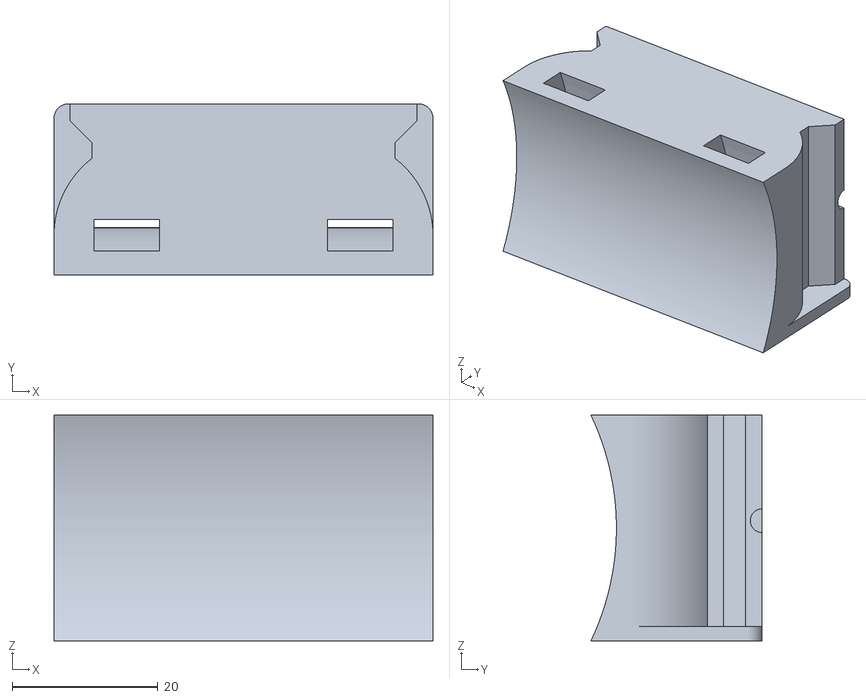
[picture p89: CAD file, 2022-05-12]
export/Mounting/TopTubeMount.stl
52.0 x 23.5 x 31.0
