openbikesensor/OpenBikeSensor3dPrintableCase/MainCase/HorizontalCase_JSN-AJ/Sattelclip.stl

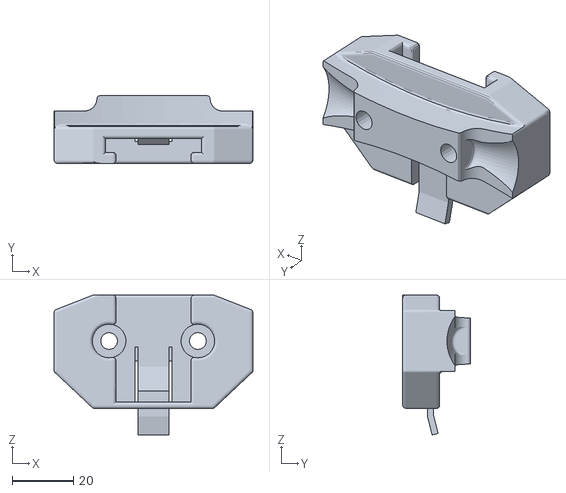
[picture p90: CAD file, 2020-10-19]
MainCase/HorizontalCase_JSN-AJ/Sattelclip.stl
65.0 x 22.1 x 45.7
