openbikesensor/OpenBikeSensor3dPrintableCase/MainCase/SnapInCase/OBS-SnapInLid.stp

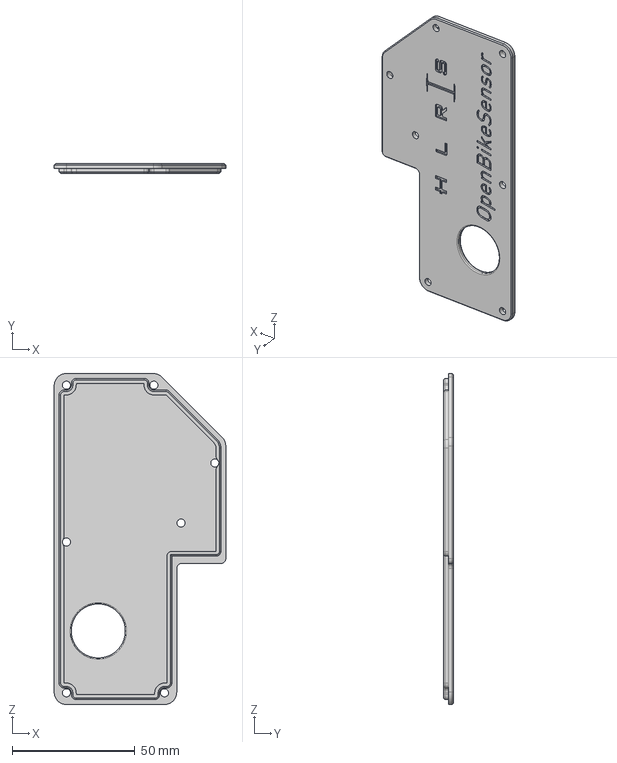
[picture p91: CAD file, 2020-06-22]
MainCase/SnapInCase/OBS-SnapInLid.stp
70.0 x 4.00 x 135.0 mm
