openbikesensor/OpenBikeSensor3dPrintableCase/MainCase/TopTubeCase/OBS-C-003-V1.step

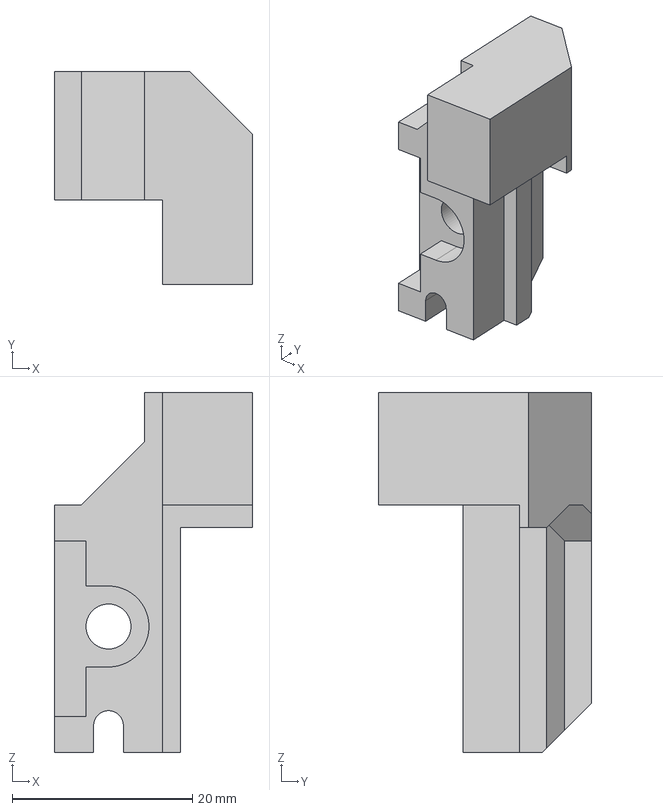
[picture p92: CAD file, 2020-04-30]
MainCase/TopTubeCase/OBS-C-003-V1.step
22.0 x 23.7 x 40.0 mm
