openbikesensor/OpenBikeSensor3dPrintableCase/DisplayCase/SnapInDisplay/DisplayClipBase.stp

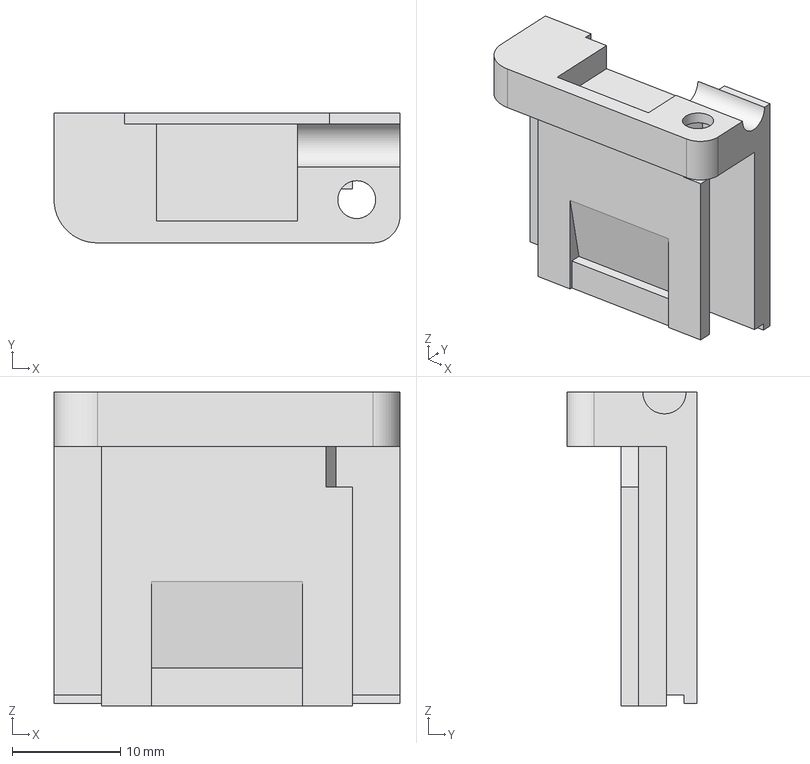
[picture p93: CAD file, 2020-07-15]
DisplayCase/SnapInDisplay/DisplayClipBase.stp
32.0 x 12.0 x 29.0 mm
