openbikesensor/OpenBikeSensor3dPrintableCase/export/Mounting/SeatPostMount.stl

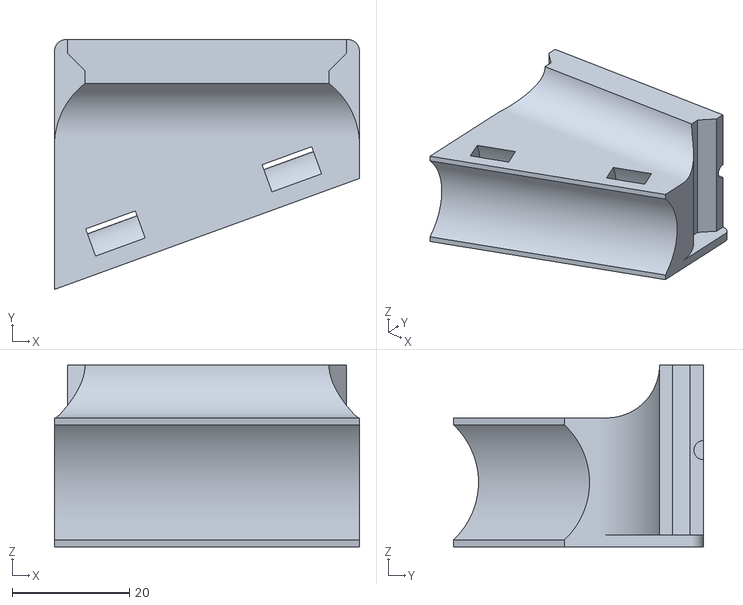
[picture p94: CAD file, 2022-05-12]
export/Mounting/SeatPostMount.stl
52.0 x 42.6 x 31.0
