openbikesensor/OpenBikeSensor3dPrintableCase/MainCase/HorizontalCase_JSN-AJ/Sattelclip_wide.stl

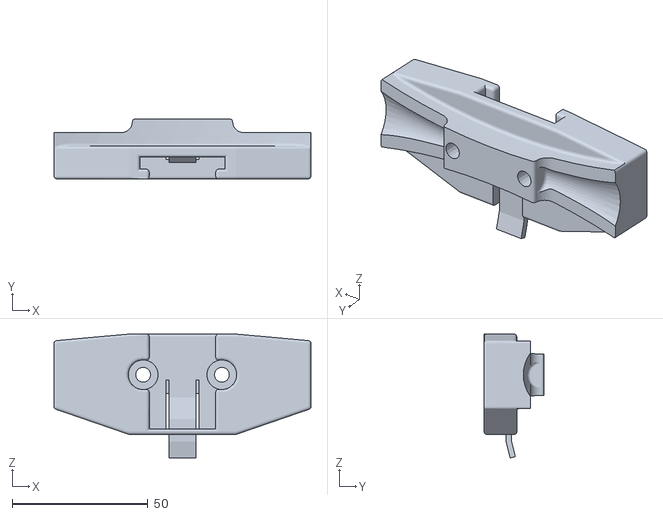
[picture p95: CAD file, 2020-10-19]
MainCase/HorizontalCase_JSN-AJ/Sattelclip_wide.stl
94.8 x 22.1 x 45.7
