openbikesensor/OpenBikeSensor3dPrintableCase/MainCase/TopTubeCase/OBS-C-002-V1.step

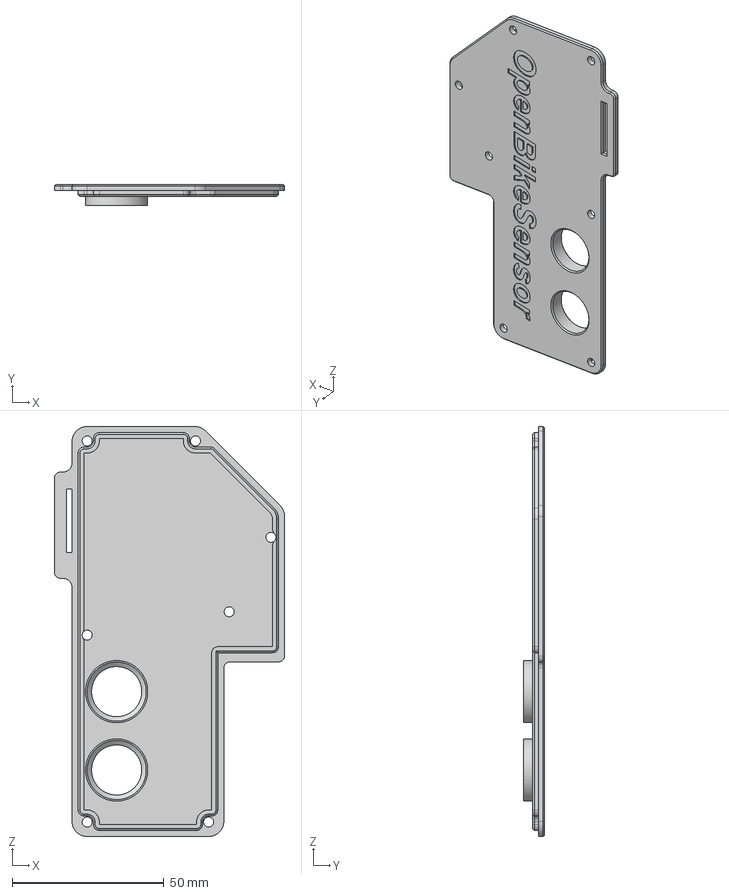
[picture p96: CAD file, 2020-04-30]
MainCase/TopTubeCase/OBS-C-002-V1.step
75.8 x 7.00 x 135.0 mm
