openbikesensor/OpenBikeSensor3dPrintableCase/MainCase/VerticalCase_JSN-AJ/OBS-Mounting-A-003_LockingPin_v0.1.3.stp

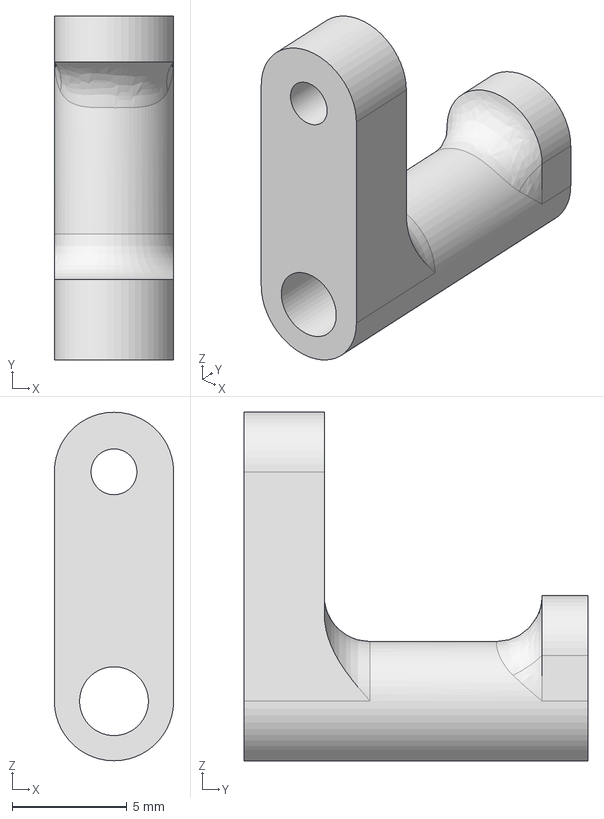
[picture p97: CAD file, 2021-06-07]
MainCase/VerticalCase_JSN-AJ/OBS-Mounting-A-003_LockingPin_v0.1.3.stp
5.20 x 15.0 x 15.2 mm
