openbikesensor/OpenBikeSensor3dPrintableCase/DisplayCase/SlideOnDisplay/OBS-Display-A-001_HeatSetInsert_Display_Top_v0.1.0.stp

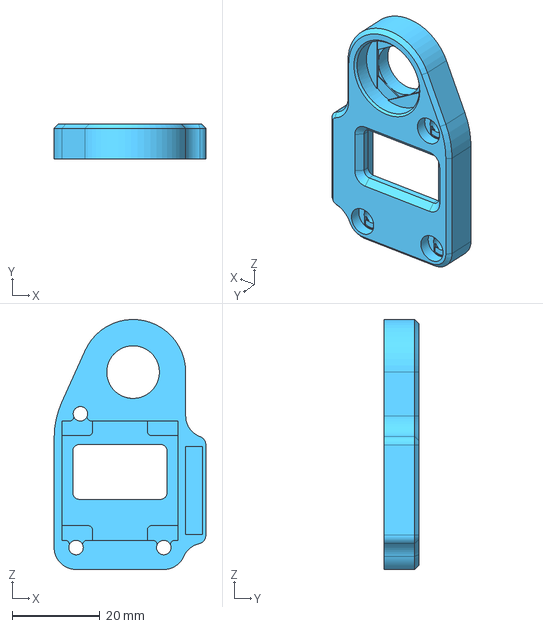
[picture p98: CAD file, 2021-04-29]
DisplayCase/SlideOnDisplay/OBS-Display-A-001_HeatSetInsert_Display_Top_v0.1.0.stp
34.6 x 8.00 x 57.0 mm
