openbikesensor/OpenBikeSensor3dPrintableCase/DisplayCase/SnapInDisplay/DisplayClip.stp

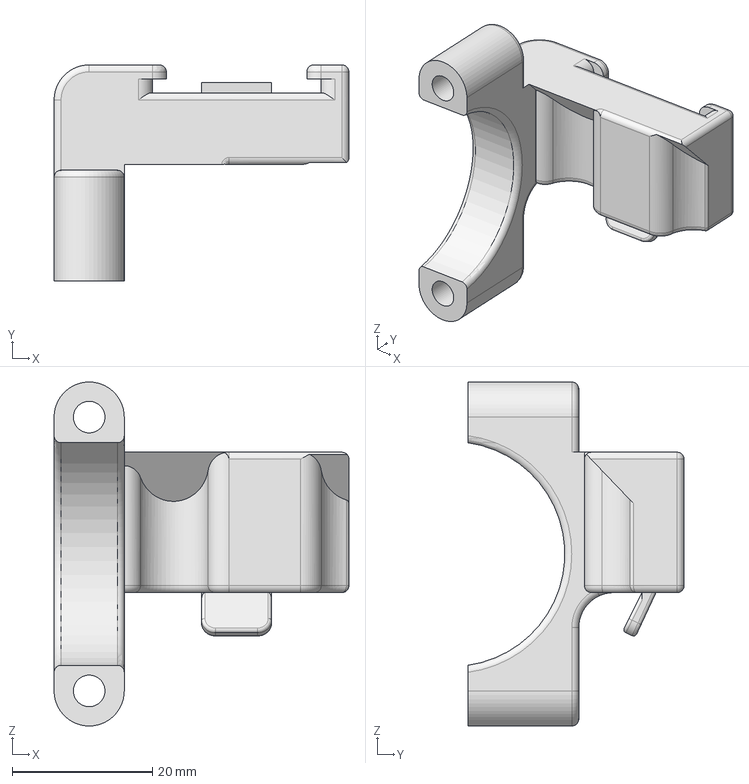
[picture p99: CAD file, 2020-07-15]
DisplayCase/SnapInDisplay/DisplayClip.stp
42.0 x 30.8 x 49.0 mm
