openbikesensor/OpenBikeSensor3dPrintableCase/export/Mounting/StandardMountAdapter.stl

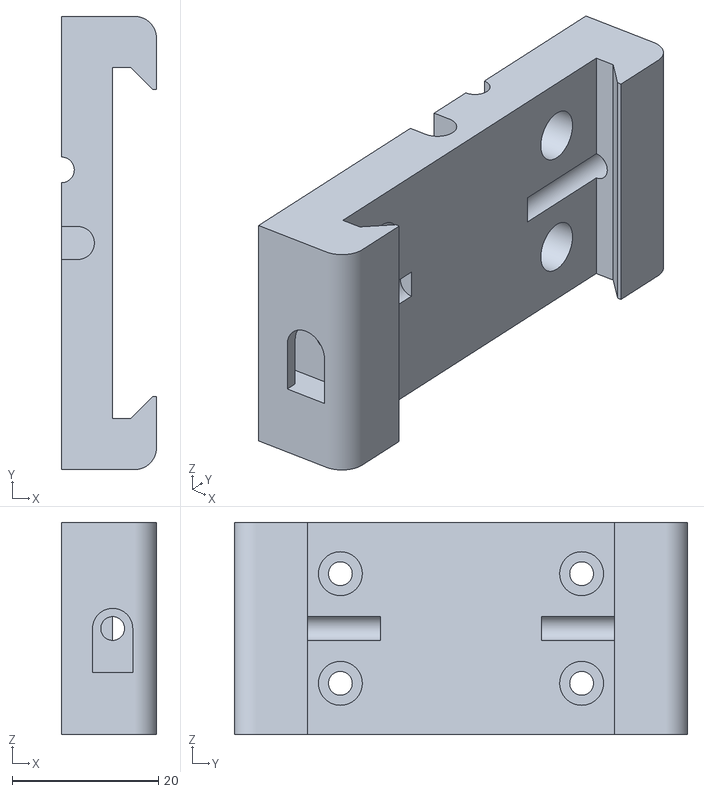
[picture p100: CAD file, 2022-03-04]
export/Mounting/StandardMountAdapter.stl
13.0 x 62.0 x 29.0
