openbikesensor/OpenBikeSensor3dPrintableCase/DisplayCase/SlideOnDisplay/OBS-Display-B-003+004_Zugentlastung_v0.1.0.stp

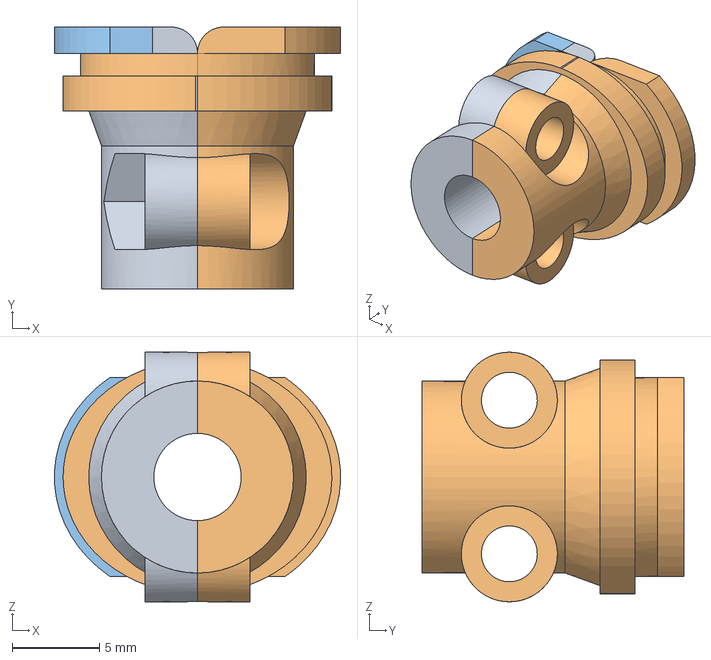
[picture p101: CAD file, 2021-04-29]
DisplayCase/SlideOnDisplay/OBS-Display-B-003+004_Zugentlastung_v0.1.0.stp
16.4 x 15.0 x 14.3 mm
