openbikesensor/OpenBikeSensor3dPrintableCase/export/Mounting/BackRiderTopRiderAdapter.stl

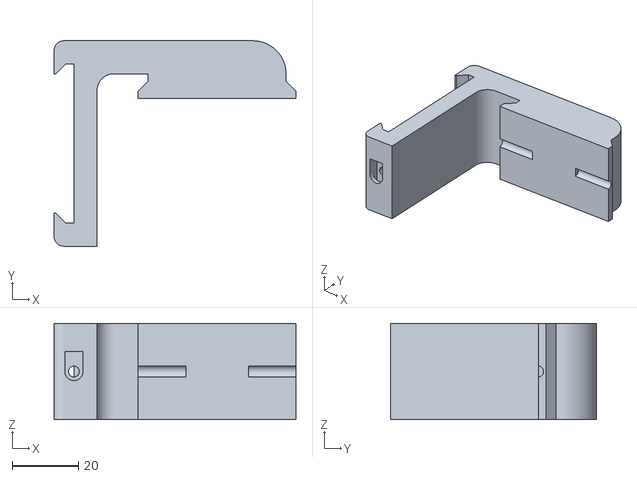
[picture p102: CAD file, 2022-03-04]
export/Mounting/BackRiderTopRiderAdapter.stl
73.0 x 62.0 x 29.0
