openbikesensor/OpenBikeSensor3dPrintableCase/export/Mounting/AttachmentCover.stl

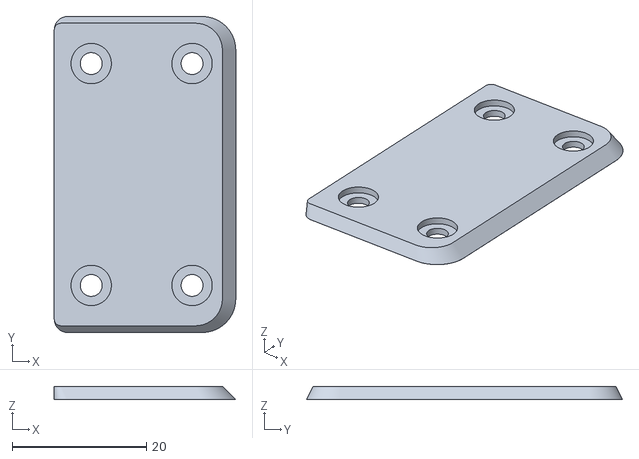
[picture p103: CAD file, 2022-03-04]
export/Mounting/AttachmentCover.stl
27.0 x 47.0 x 2.00
