openbikesensor/OpenBikeSensor3dPrintableCase/DisplayCase/SlideOnDisplay/OBS-Display-B-007_Unterschale_v0.1.0.stp

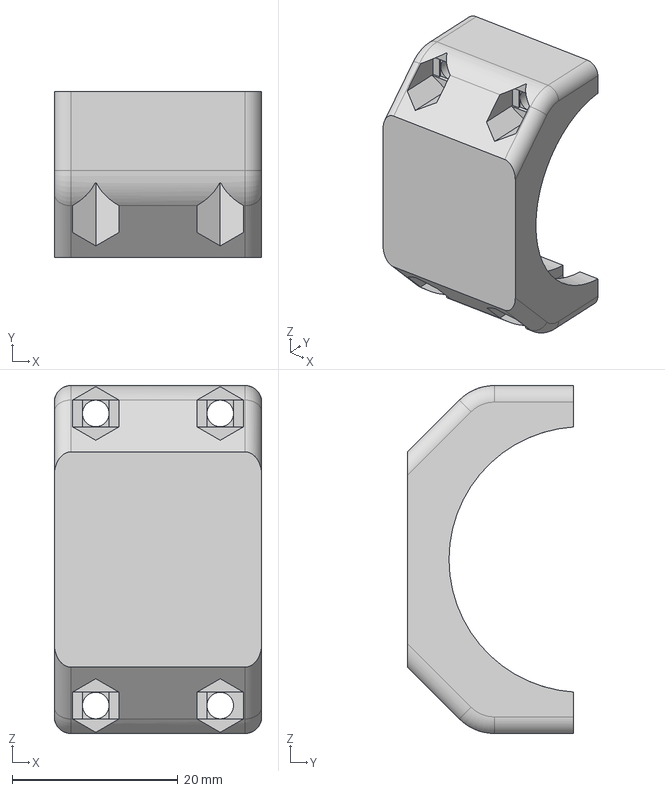
[picture p104: CAD file, 2021-04-29]
DisplayCase/SlideOnDisplay/OBS-Display-B-007_Unterschale_v0.1.0.stp
25.0 x 20.0 x 41.9 mm
