openbikesensor/OpenBikeSensor3dPrintableCase/DisplayCase/SlideOnDisplay/OBS-D-003 v14_Schlauchschelle_hybride.step

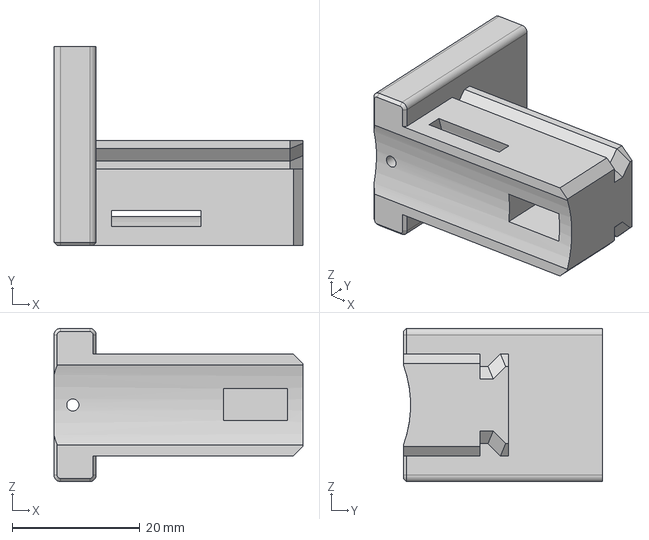
[picture p105: CAD file, 2021-03-11]
DisplayCase/SlideOnDisplay/OBS-D-003 v14_Schlauchschelle_hybride.step
39.0 x 31.2 x 24.0 mm
