openbikesensor/OpenBikeSensor3dPrintableCase/MainCase/VerticalCase_JSN-AJ/OBS-Mounting-A-002_StandardSeatPostMount_v0.1.1.stp

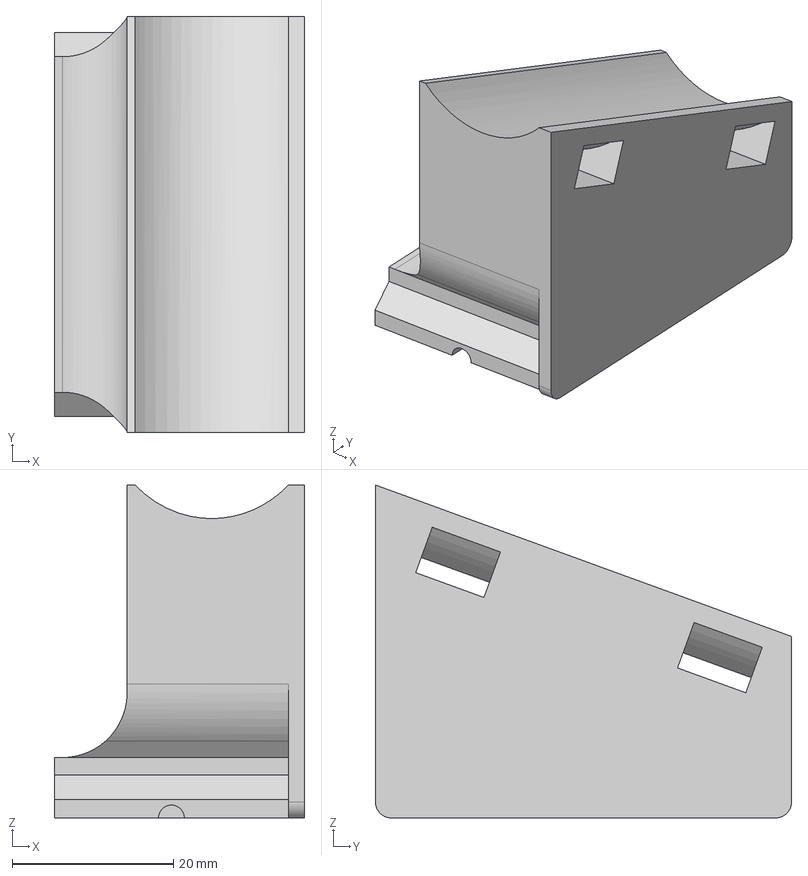
[picture p107: CAD file, 2021-04-21]
MainCase/VerticalCase_JSN-AJ/OBS-Mounting-A-002_StandardSeatPostMount_v0.1.1.stp
31.0 x 51.6 x 41.3 mm
