openbikesensor/OpenBikeSensor3dPrintableCase/DisplayCase/SlideOnDisplay/OBS-D-006 v11_25_4.stl

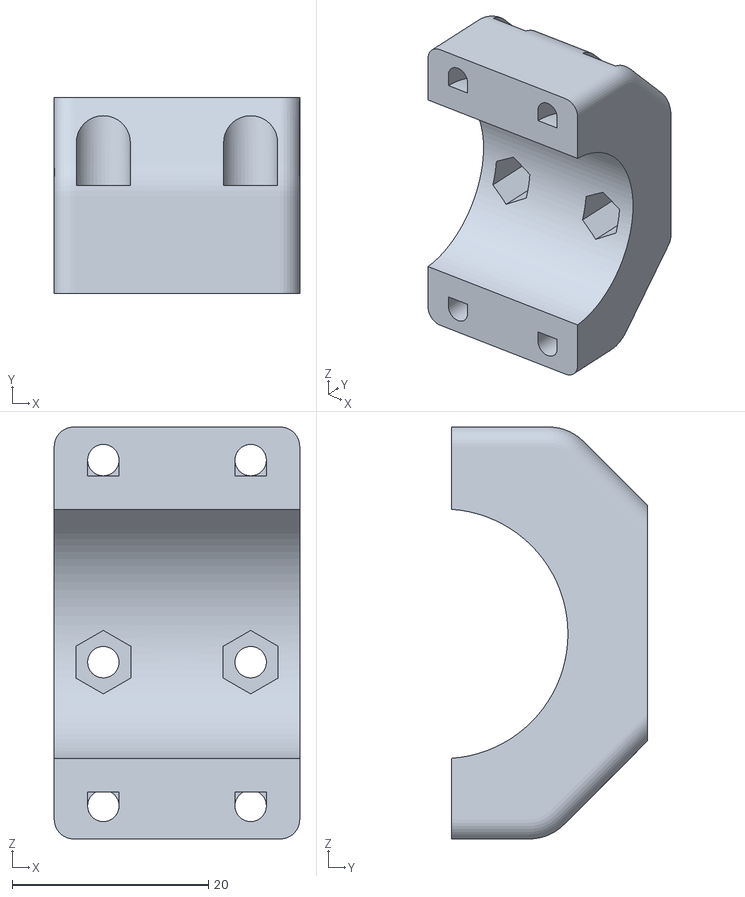
[picture p108: CAD file, 2020-12-29]
DisplayCase/SlideOnDisplay/OBS-D-006 v11_25_4.stl
25.0 x 20.0 x 41.9
