openbikesensor/OpenBikeSensor3dPrintableCase/MainCase/VerticalCase_JSN-AJ/OBS-Mounting-A-001_StandardOBSMount_v0.1.1.stp

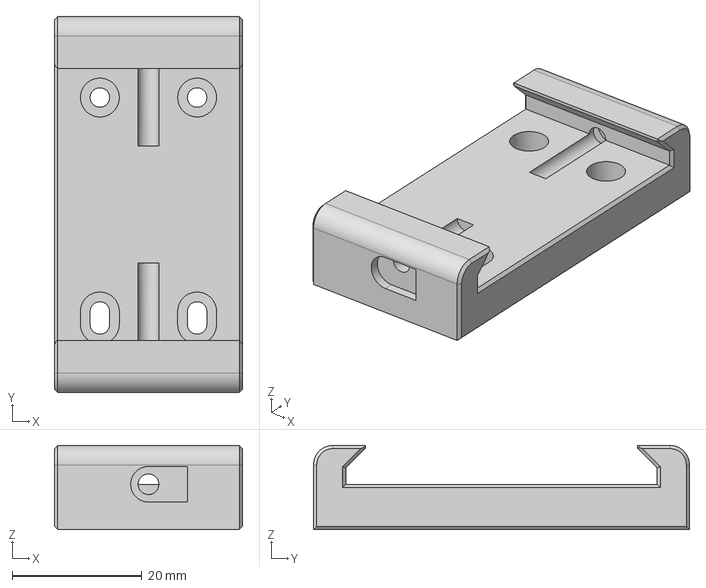
[picture p109: CAD file, 2021-04-21]
MainCase/VerticalCase_JSN-AJ/OBS-Mounting-A-001_StandardOBSMount_v0.1.1.stp
29.0 x 58.0 x 13.0 mm
