openbikesensor/OpenBikeSensor3dPrintableCase/DisplayCase/SlideOnDisplay/OBS-A-002-AlternativeMount22mmTop.stl

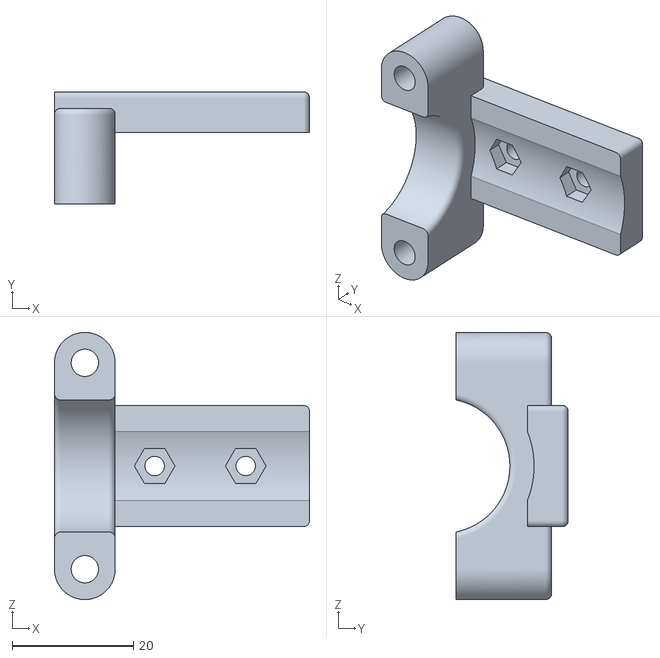
[picture p110: CAD file, 2020-11-21]
DisplayCase/SlideOnDisplay/OBS-A-002-AlternativeMount22mmTop.stl
42.0 x 18.5 x 44.0
