openbikesensor/OpenBikeSensor3dPrintableCase/MainCase/VerticalCase_JSN-AJ/OBS-Mounting-B-002_TopTubeMount.stp

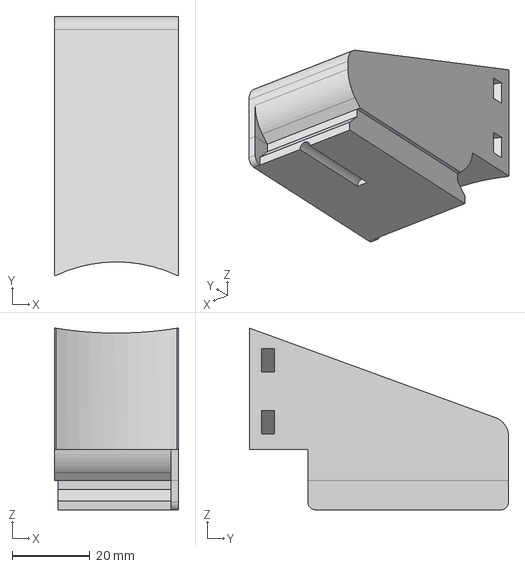
[picture p111: CAD file, 2021-04-21]
MainCase/VerticalCase_JSN-AJ/OBS-Mounting-B-002_TopTubeMount.stp
32.0 x 66.6 x 46.7 mm
