openbikesensor/OpenBikeSensor3dPrintableCase/DisplayCase/SlideOnDisplay/OBS-D-004 v6.step

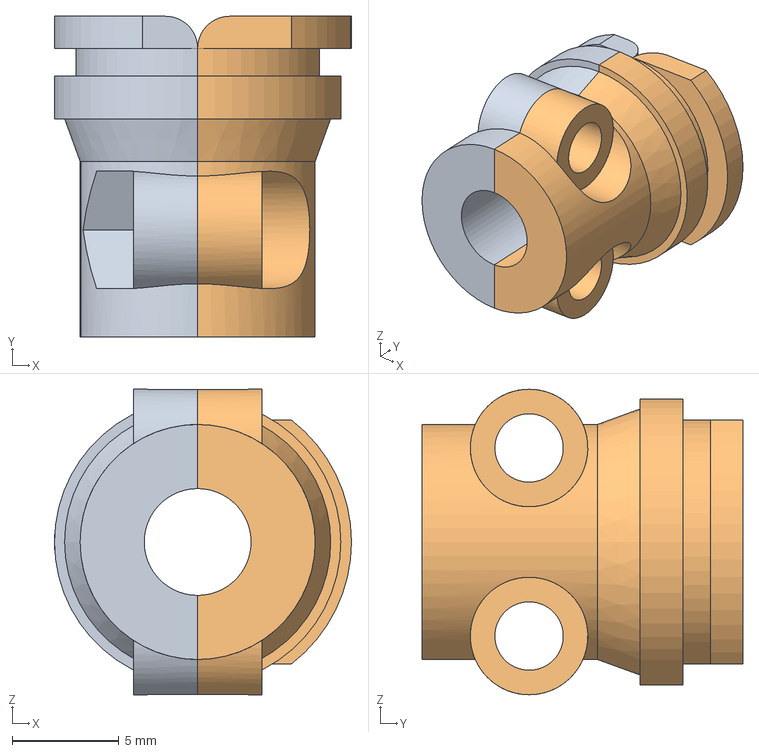
[picture p112: CAD file, 2020-10-05]
DisplayCase/SlideOnDisplay/OBS-D-004 v6.step
13.9 x 15.0 x 14.3 mm
