openbikesensor/OpenBikeSensor3dPrintableCase/MainCase/VerticalCase_JSN-AJ/OBS-Mounting-C-002_ExtendedSeatPostMount.stp

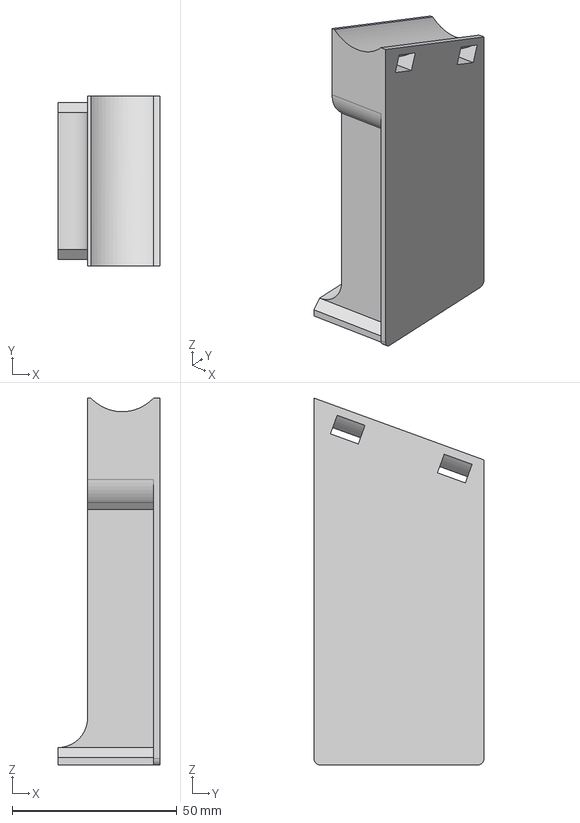
[picture p113: CAD file, 2021-03-06]
MainCase/VerticalCase_JSN-AJ/OBS-Mounting-C-002_ExtendedSeatPostMount.stp
31.0 x 51.6 x 111.3 mm
