openbikesensor/OpenBikeSensor3dPrintableCase/DisplayCase/SlideOnDisplay/OBS-D-003 v10.step

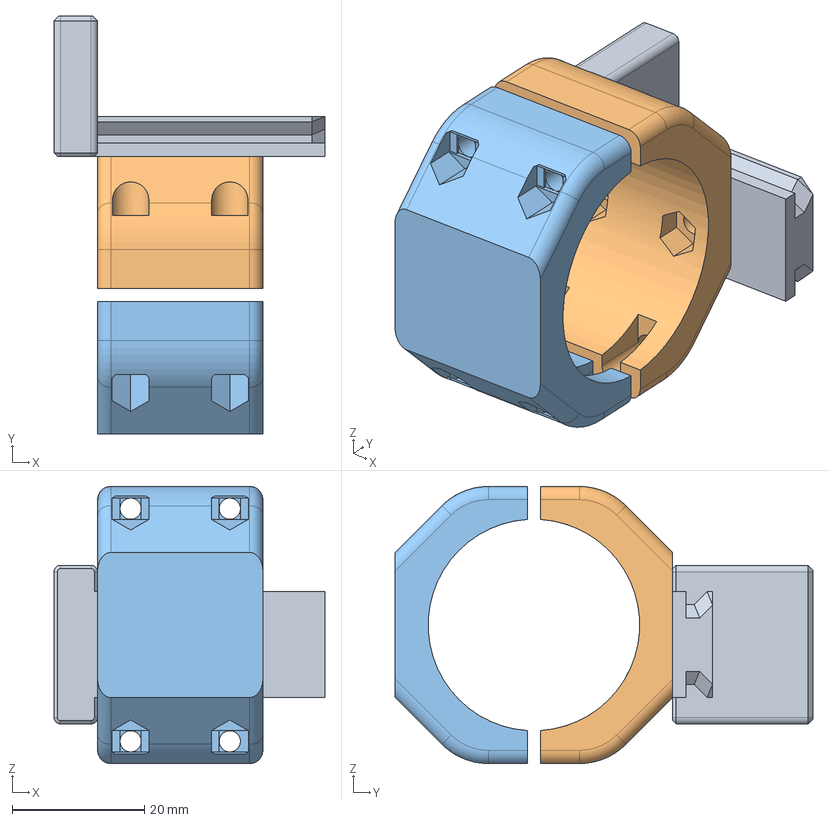
[picture p114: CAD file, 2020-10-05]
DisplayCase/SlideOnDisplay/OBS-D-003 v10.step
41.0 x 63.2 x 41.9 mm
