openbikesensor/OpenBikeSensor3dPrintableCase/src/Calibration/ScrewHoles.scad

use  <../../lib/Calibration.scad>

HolePatternM3Screw();
