openbikesensor/OpenBikeSensor3dPrintableCase/src/Mounting/DisplayMagnetDummy.scad

include <../../variables.scad>
use <../../lib/utils.scad>

cube([HandlebarRail_stopblock_magnet_height-2*default_clearance, HandlebarRail_stopblock_magnet_width-2*default_clearance, HandlebarRail_stopblock_magnet_thickness-2*default_clearance]);
