openbikesensor/OpenBikeSensor3dPrintableCase/render/thumbnails/Calibration/HexNuts.png

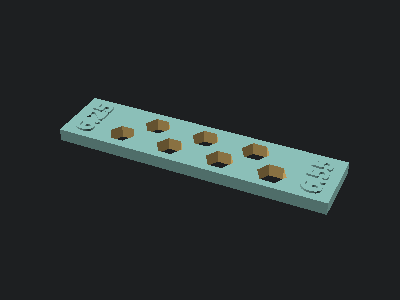
render/thumbnails/Calibration/HexNuts.png
